Kubiczek36/TKC/imgs/bw_schema_okularu.jpeg

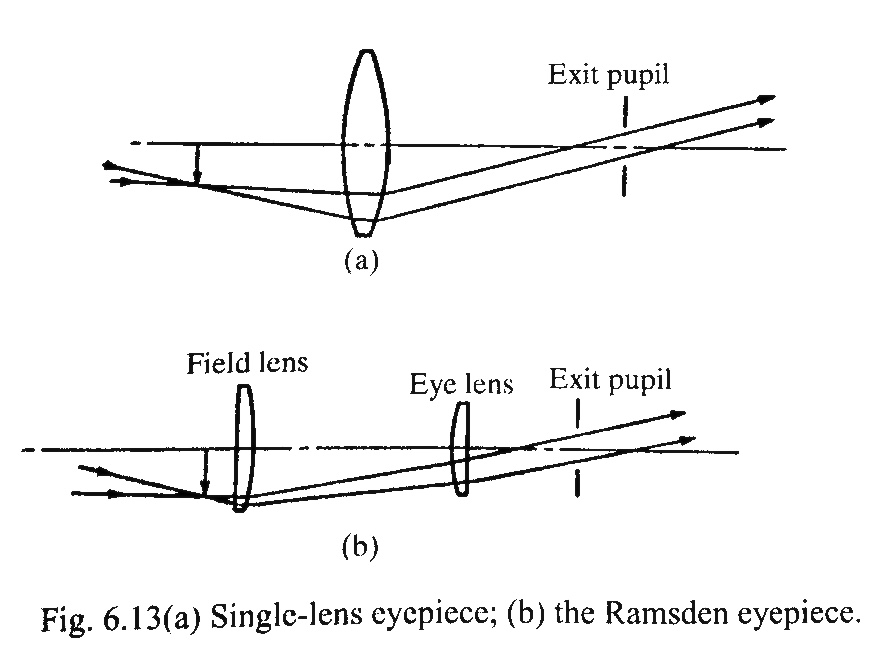
imgs/bw_schema_okularu.jpeg
