Kubiczek36/TKC/imgs/clony.png

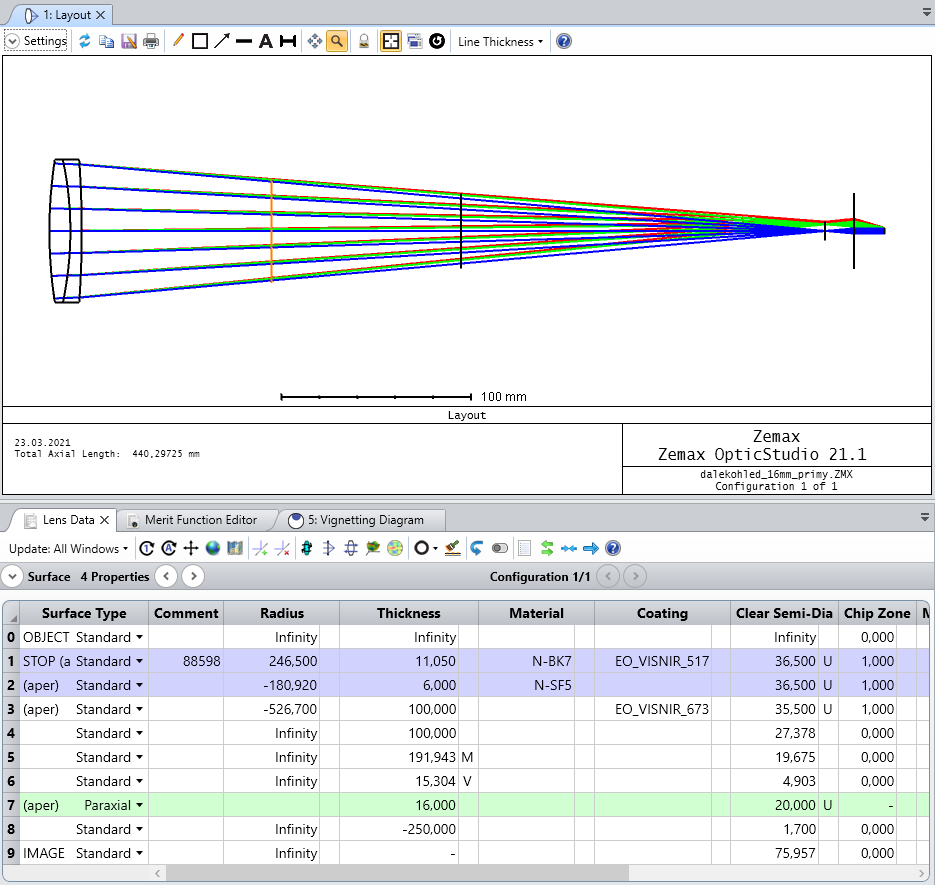
imgs/clony.png
