Kubiczek36/TKC/imgs/clony_1.png

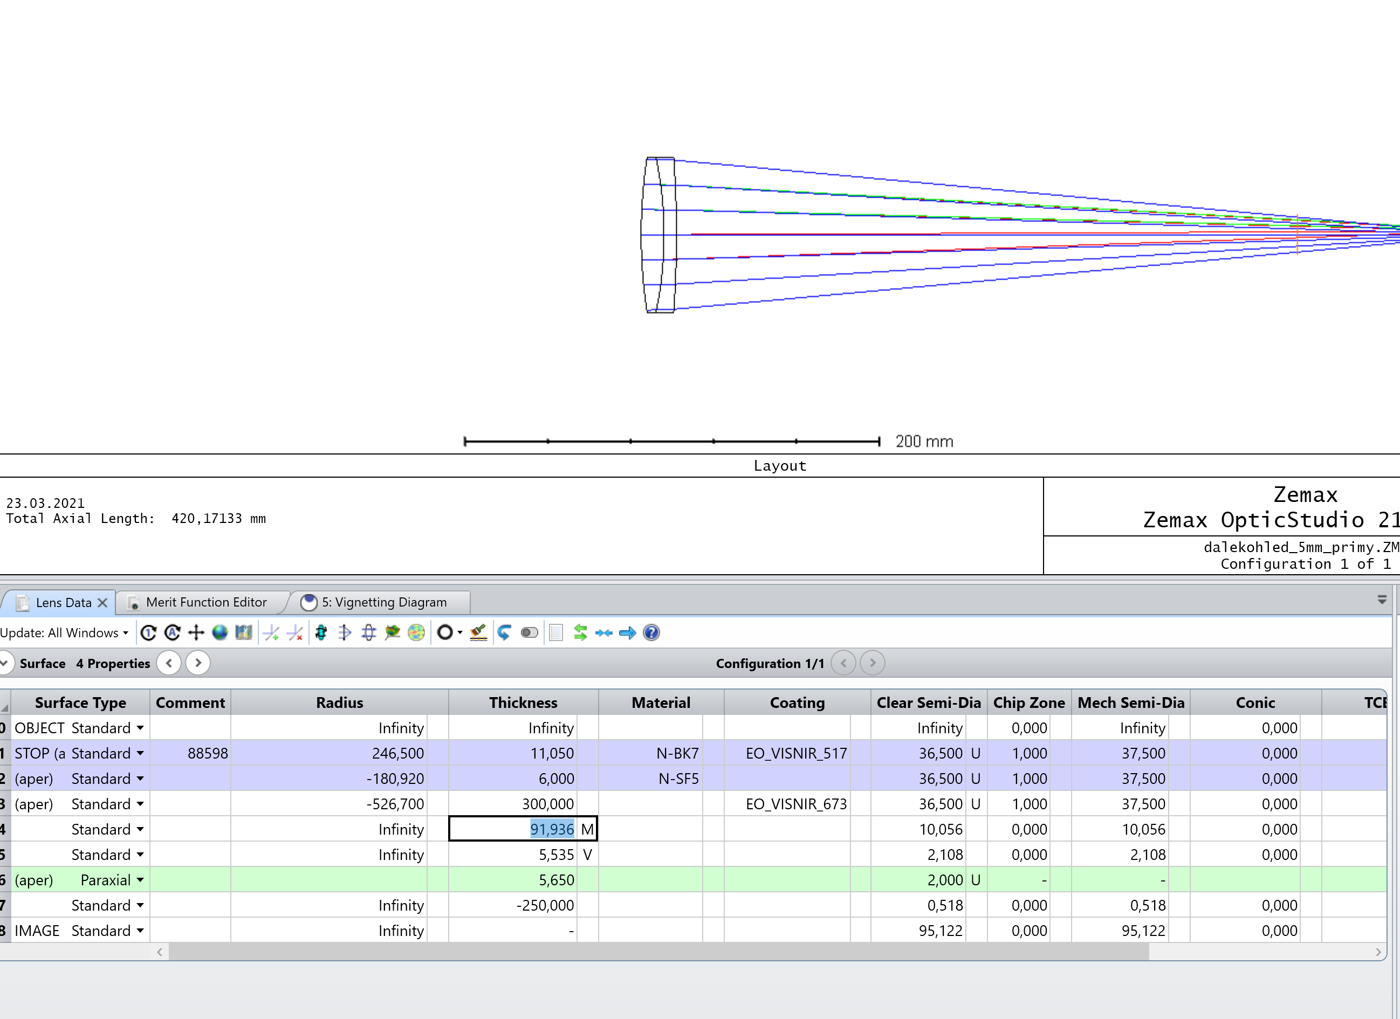
imgs/clony_1.png
