Kubiczek36/TKC/imgs/FFTMTF_5mm.png

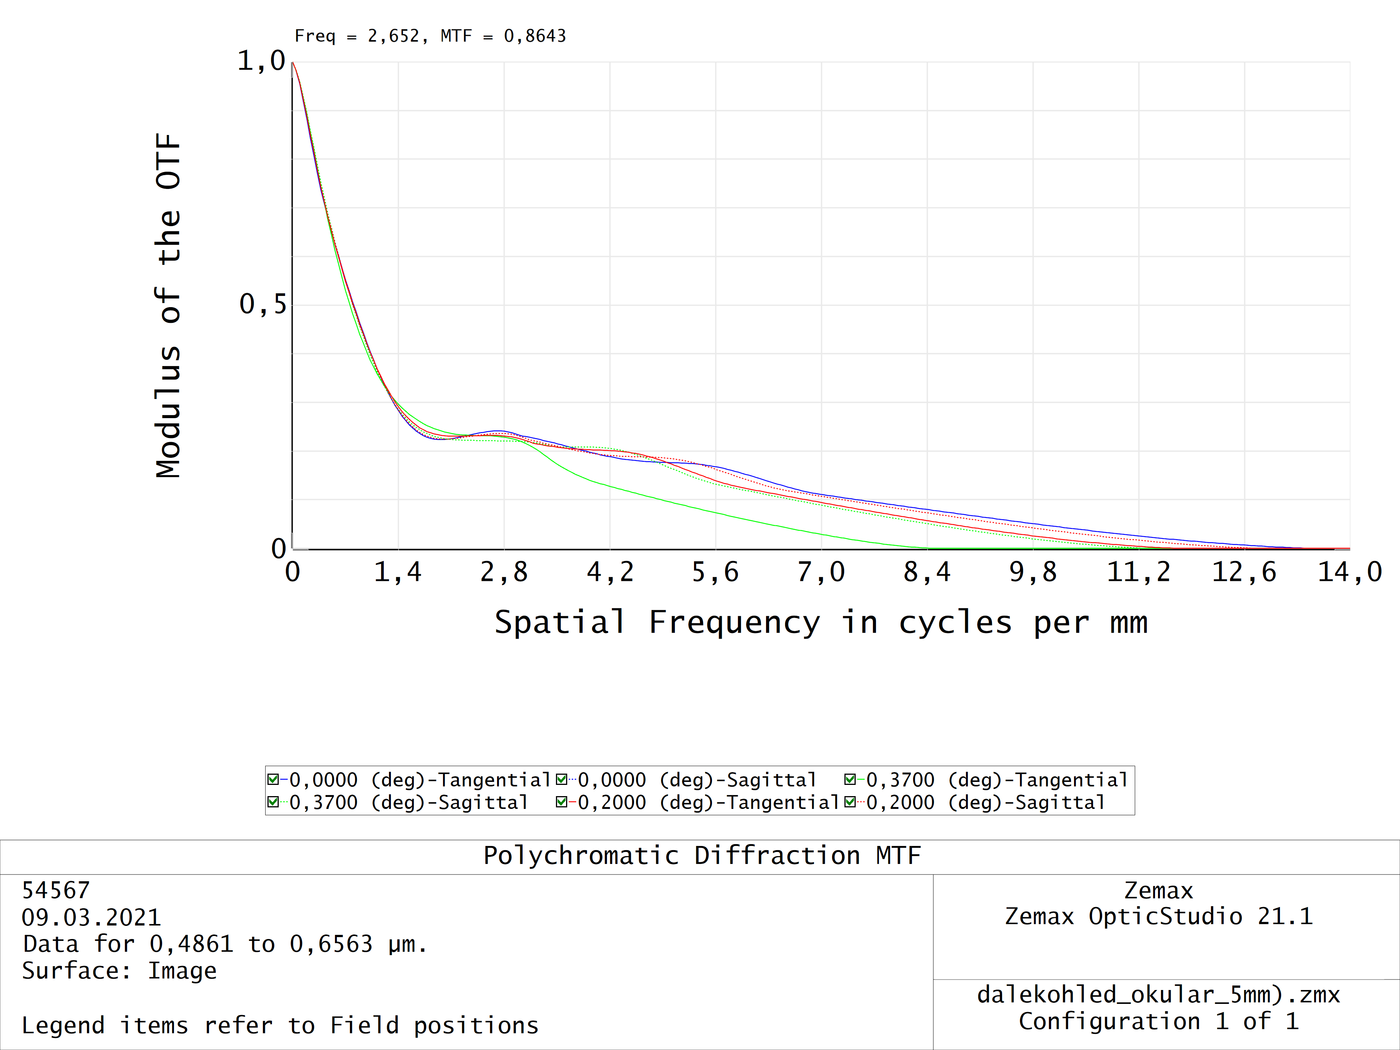
imgs/FFTMTF_5mm.png
