Kubiczek36/TKC/imgs/FFTMTFvsField_dublet_prez.png

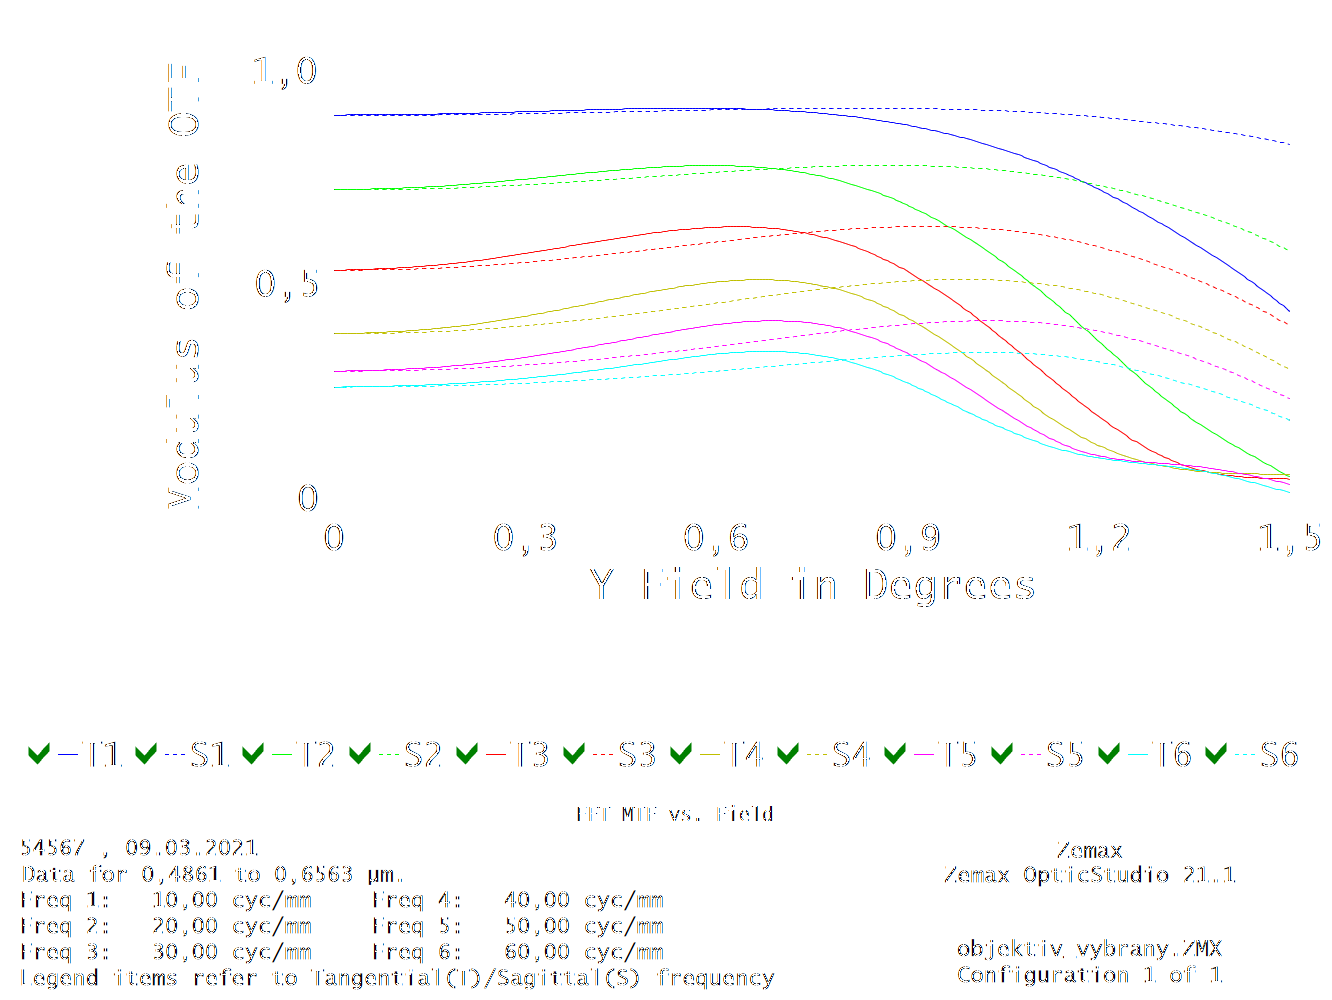
imgs/FFTMTFvsField_dublet_prez.png
