Kubiczek36/TKC/imgs/fh_dalekohledove_ok.jpeg

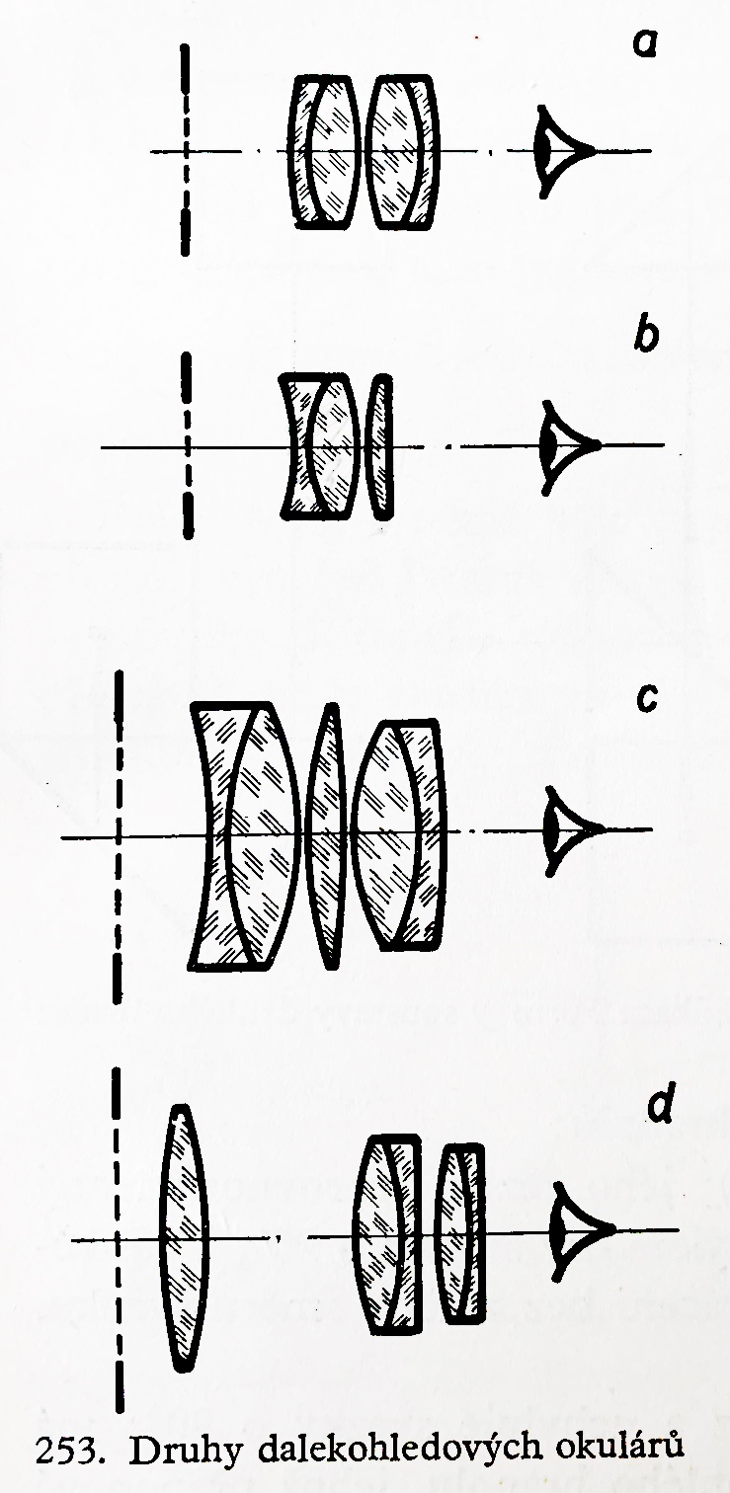
imgs/fh_dalekohledove_ok.jpeg
