Kubiczek36/TKC/imgs/fh_mikroskopove_okulary.jpeg

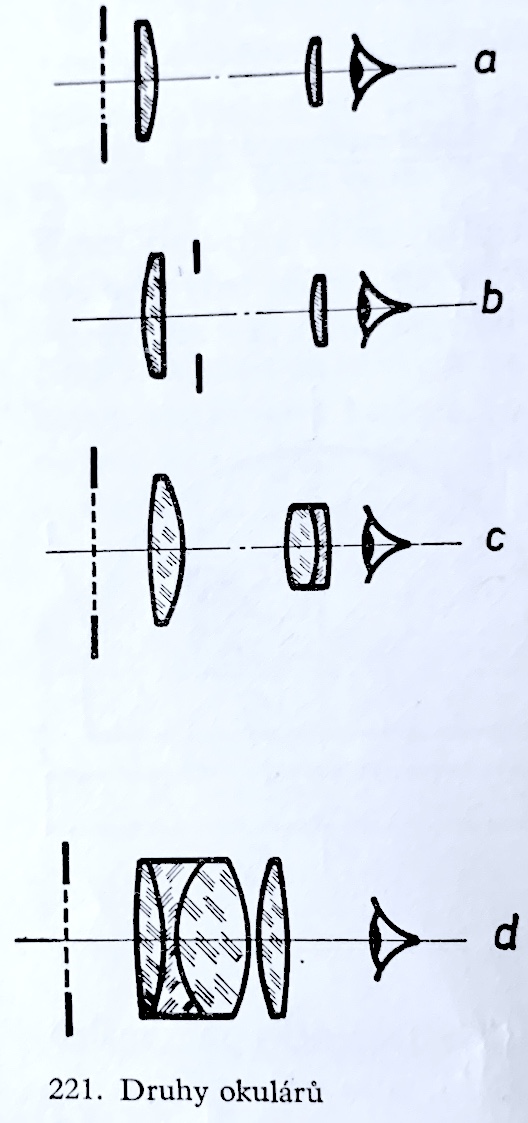
imgs/fh_mikroskopove_okulary.jpeg
