Kubiczek36/TKC/imgs/field_curv_prez.png

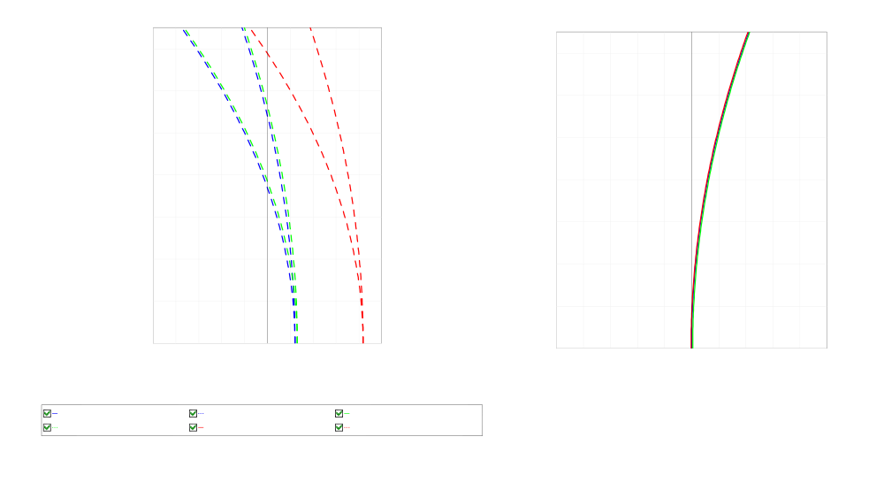
imgs/field_curv_prez.png
