Kubiczek36/TKC/imgs/Layout.png

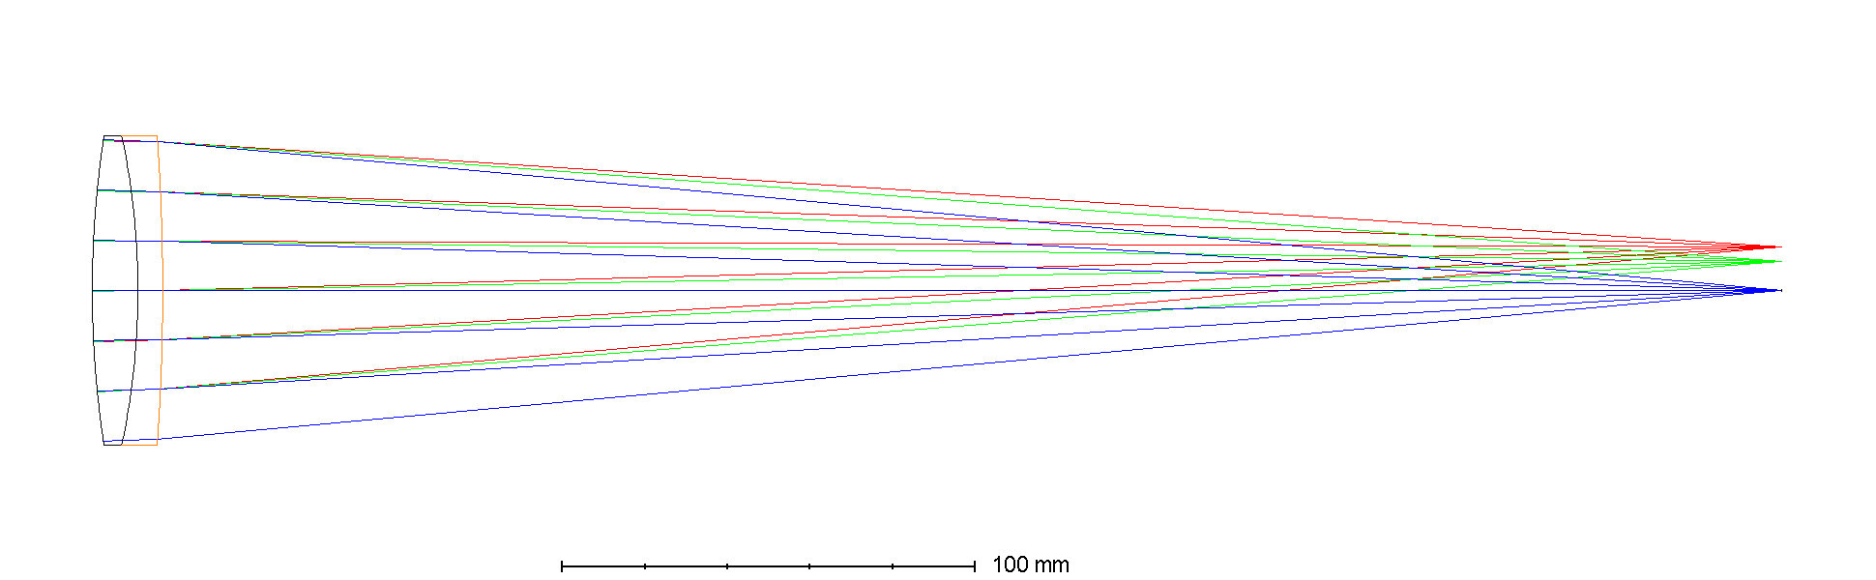
imgs/Layout.png
