Kubiczek36/TKC/imgs/leica_porovnani.png

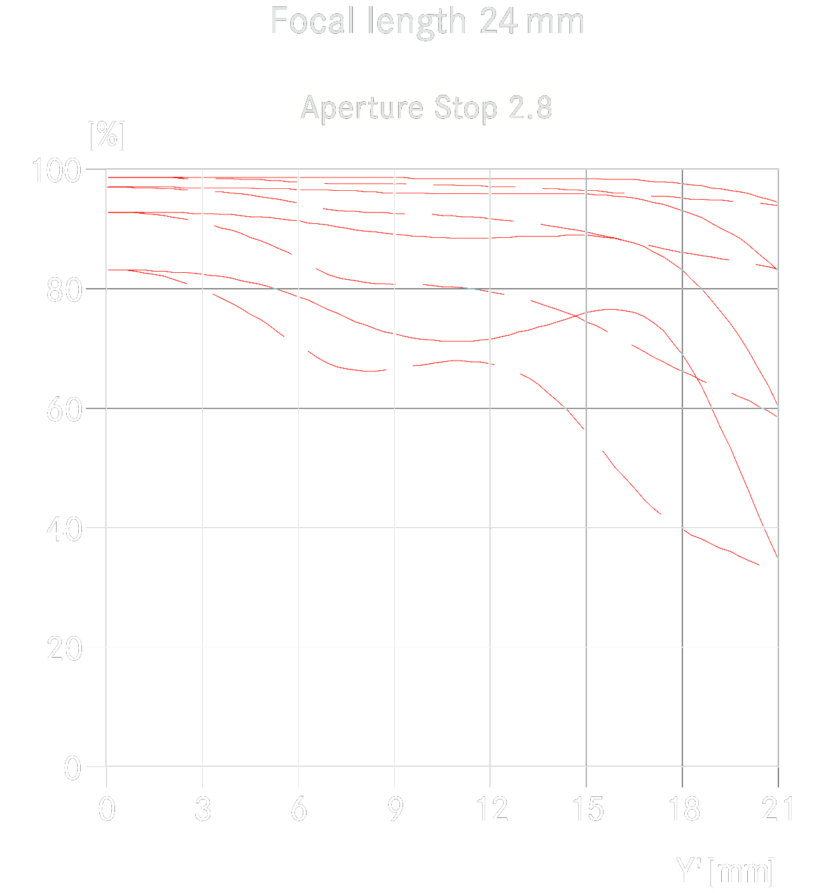
imgs/leica_porovnani.png
