Kubiczek36/TKC/imgs/nakres.jpg

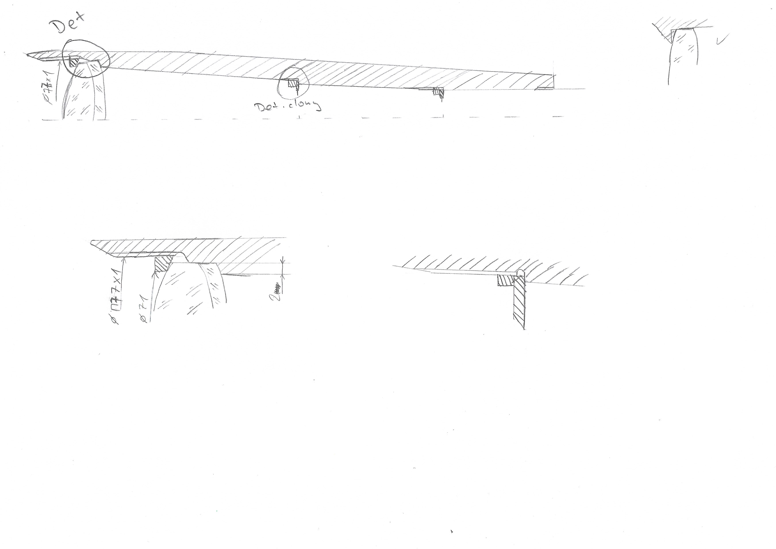
imgs/nakres.jpg
