Kubiczek36/TKC/imgs/preview.JPG

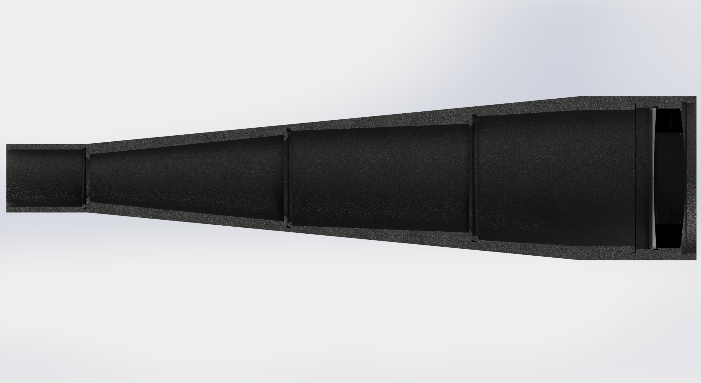
imgs/preview.JPG
