Kubiczek36/TKC/imgs/render_4.JPG

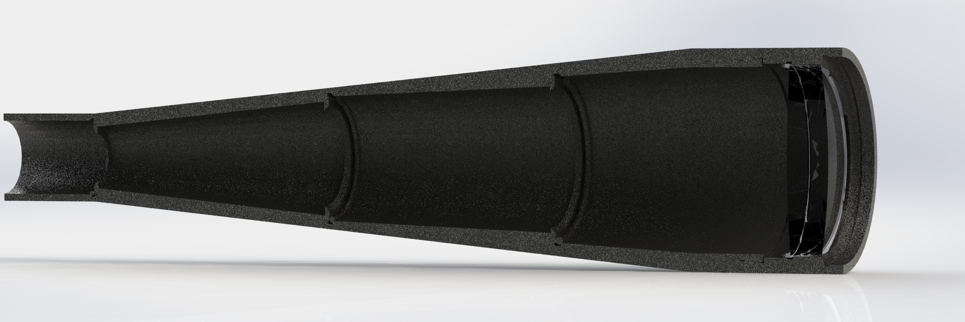
imgs/render_4.JPG
