Kubiczek36/TKC/imgs/render_6.JPG

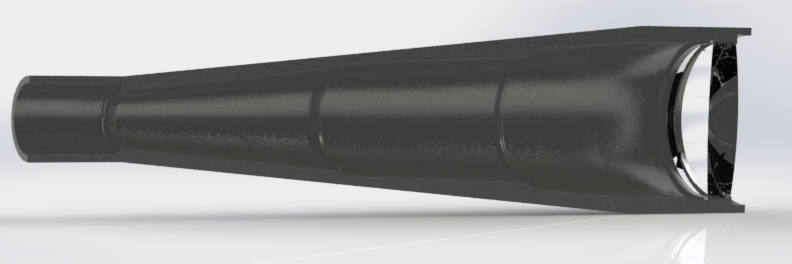
imgs/render_6.JPG
