Kubiczek36/TKC/imgs/render_7.JPG

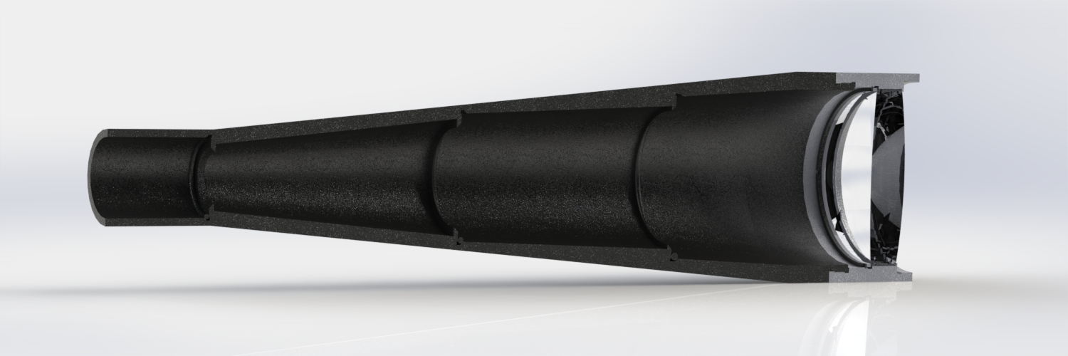
imgs/render_7.JPG
