Kubiczek36/TKC/imgs/render_final_foto.png

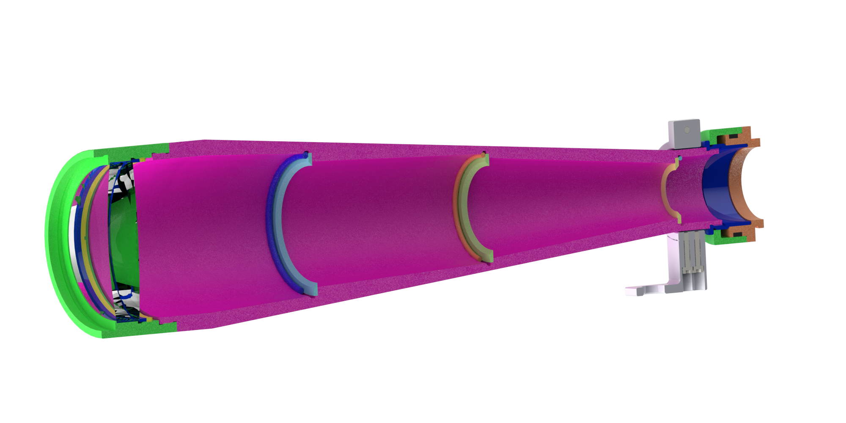
imgs/render_final_foto.png
