Kubiczek36/TKC/imgs/render_final_oko.png

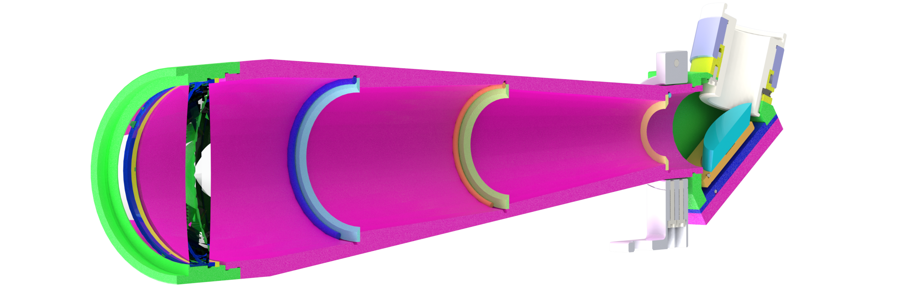
imgs/render_final_oko.png
