Kubiczek36/TKC/imgs/render_foto_vysuv.png

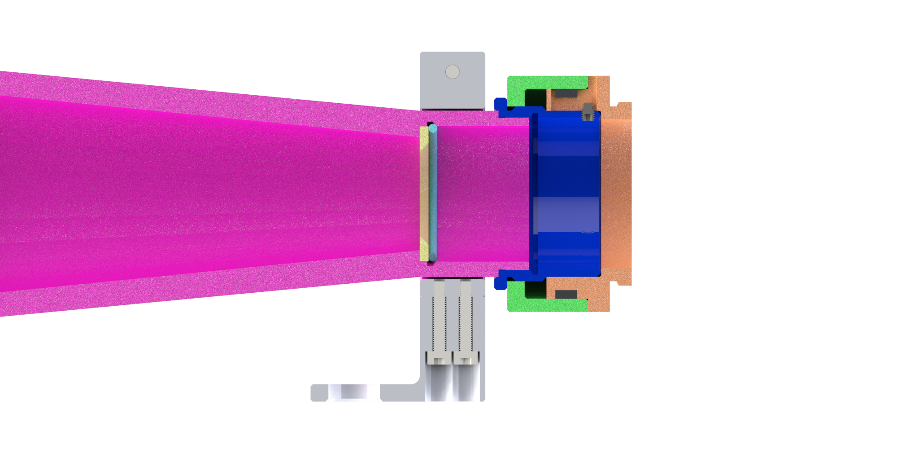
imgs/render_foto_vysuv.png
