Kubiczek36/TKC/imgs/render_tribod_mechanizmus.png

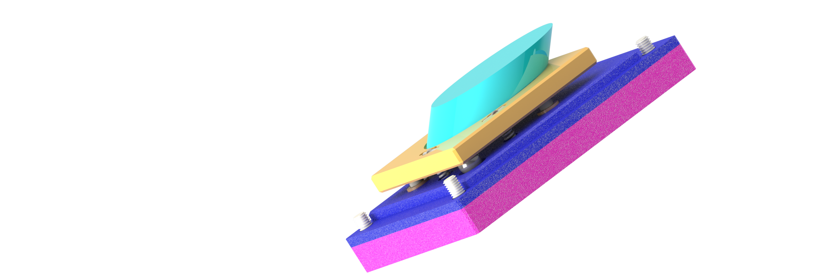
imgs/render_tribod_mechanizmus.png
