Kubiczek36/TKC/imgs/render_vysuv.png

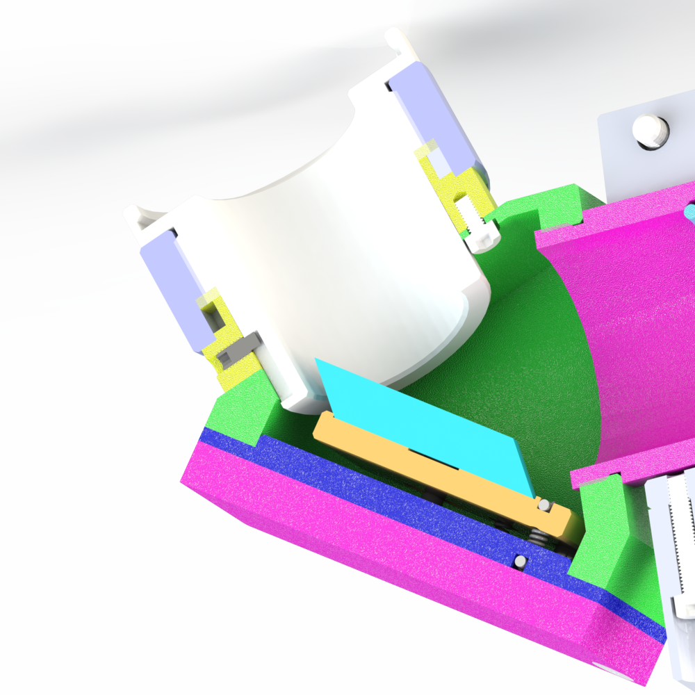
imgs/render_vysuv.png
