Kubiczek36/TKC/imgs/ShadedModel.png

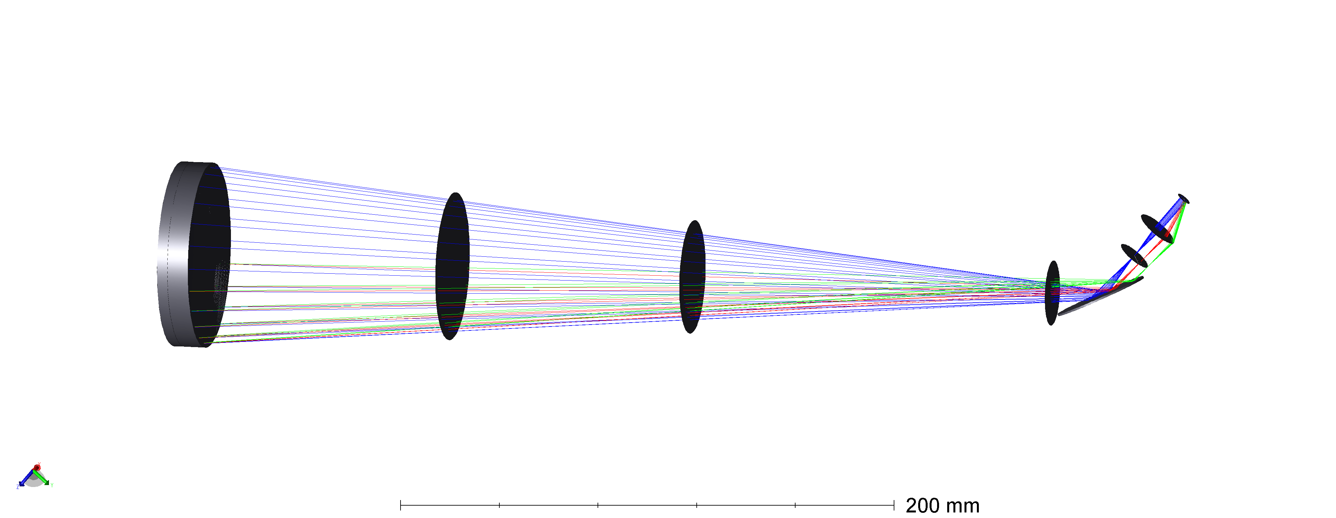
imgs/ShadedModel.png
