Kubiczek36/TKC/imgs/ShadedModel_1.png

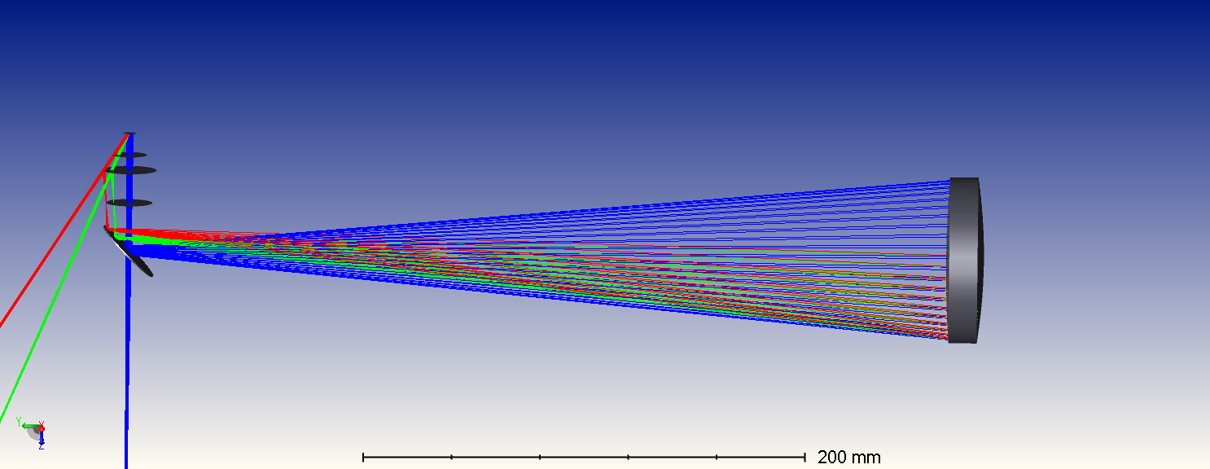
imgs/ShadedModel_1.png
