Kubiczek36/TKC/imgs/ShadedModel_high_res.png

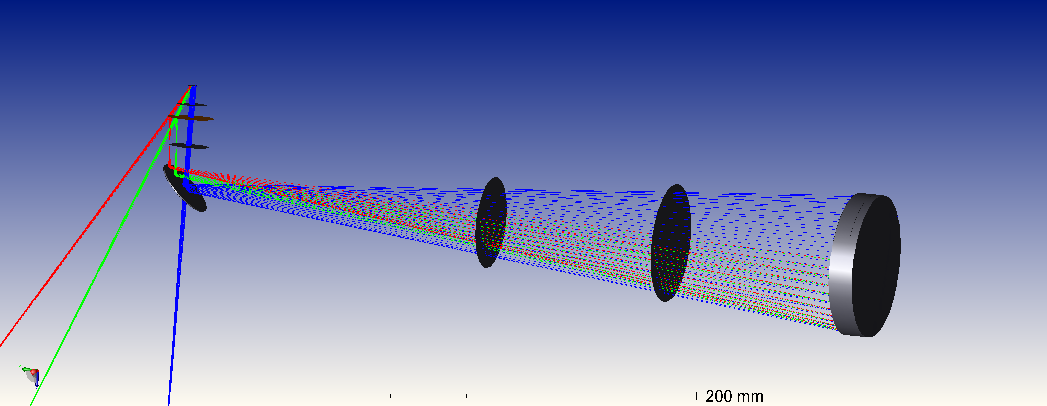
imgs/ShadedModel_high_res.png
