Kubiczek36/TKC/imgs/SpotDiagram_5_mm.png

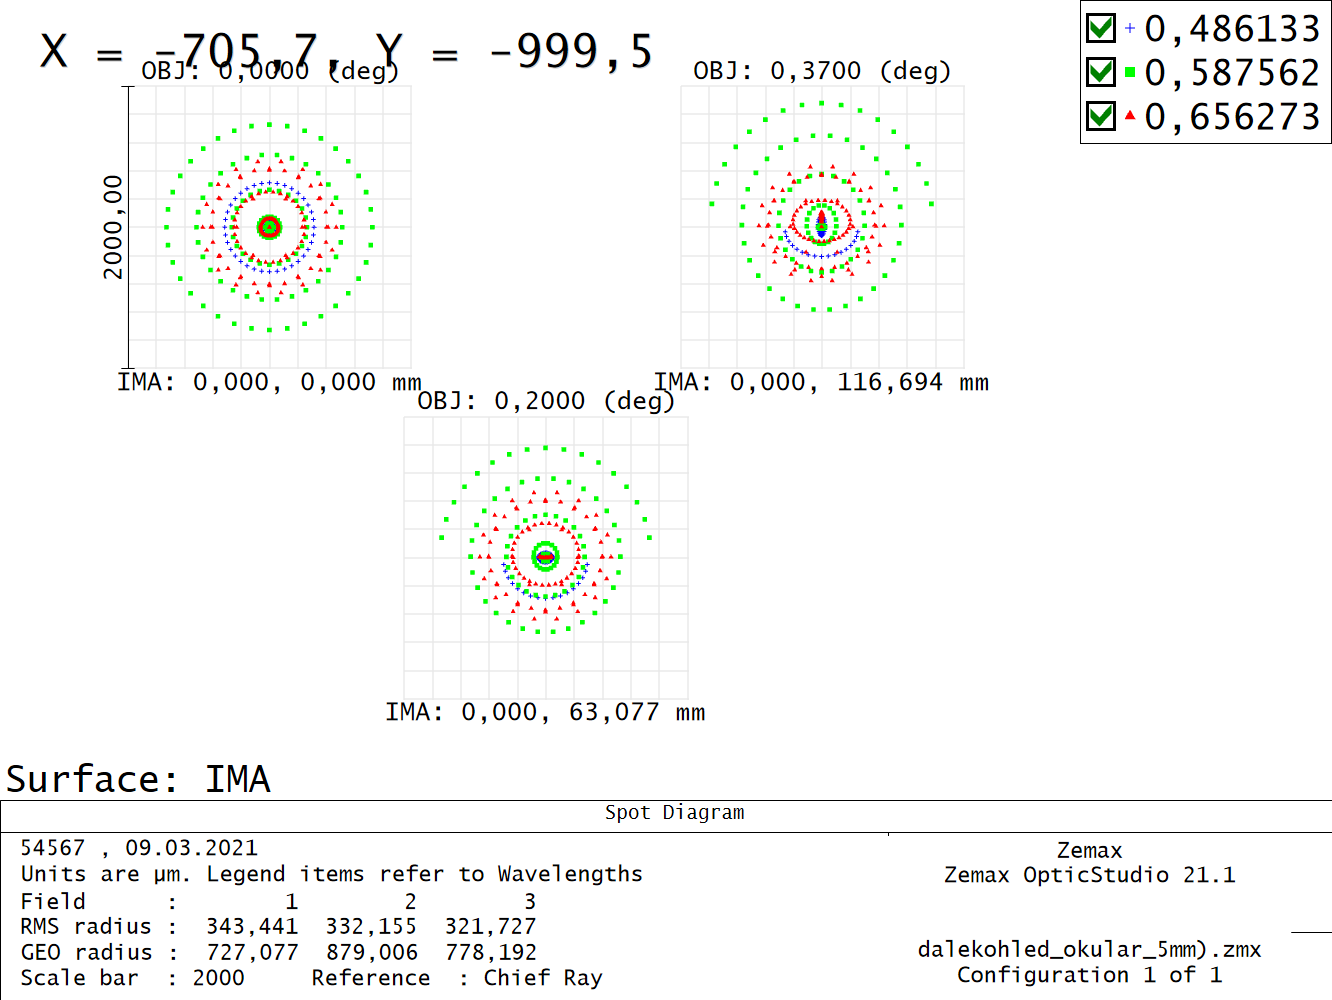
imgs/SpotDiagram_5_mm.png
