Kubiczek36/TKC/imgs/SpotDiagram_obraz_objektivu.png

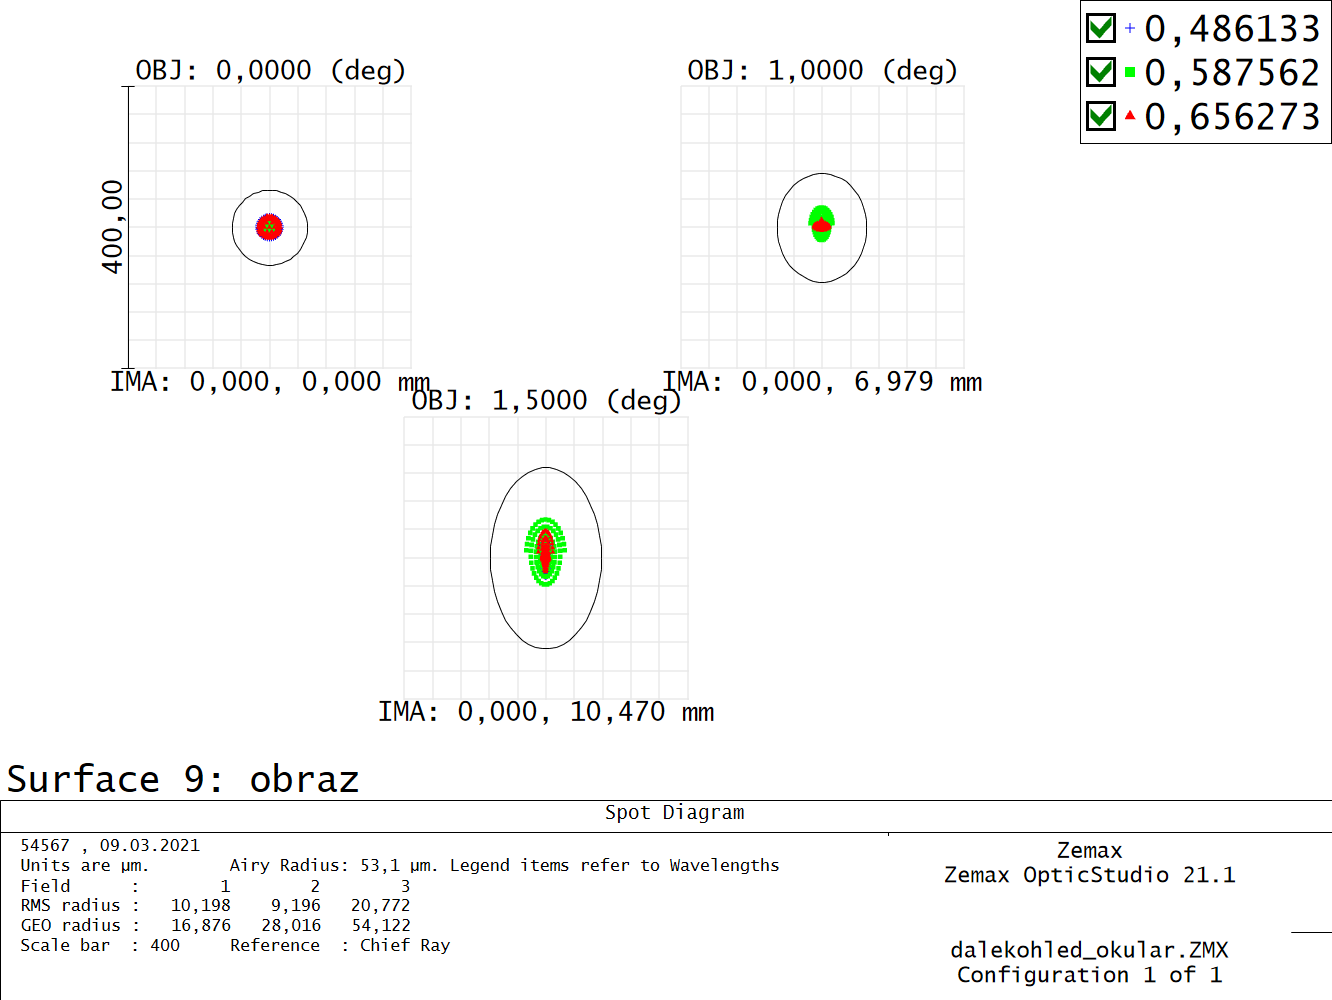
imgs/SpotDiagram_obraz_objektivu.png
