Kubiczek36/TKC/imgs/tubus_+_objektiv_+_polotovary.jpg

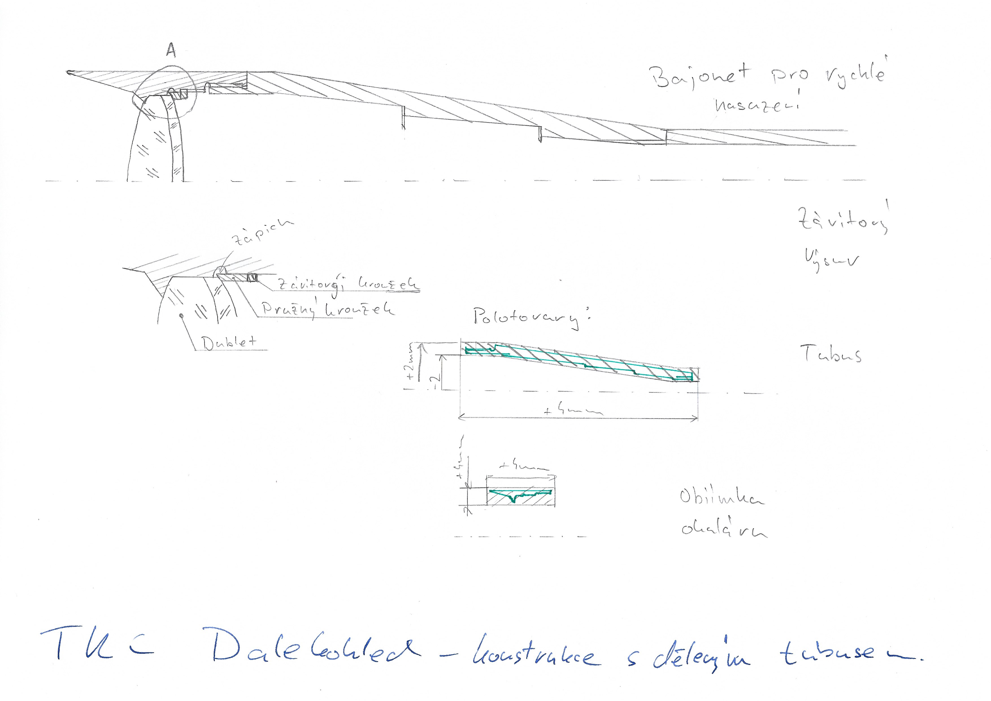
imgs/tubus_+_objektiv_+_polotovary.jpg
