Kubiczek36/TKC/imgs/tubus_s_objektivovou_objimkou.jpg

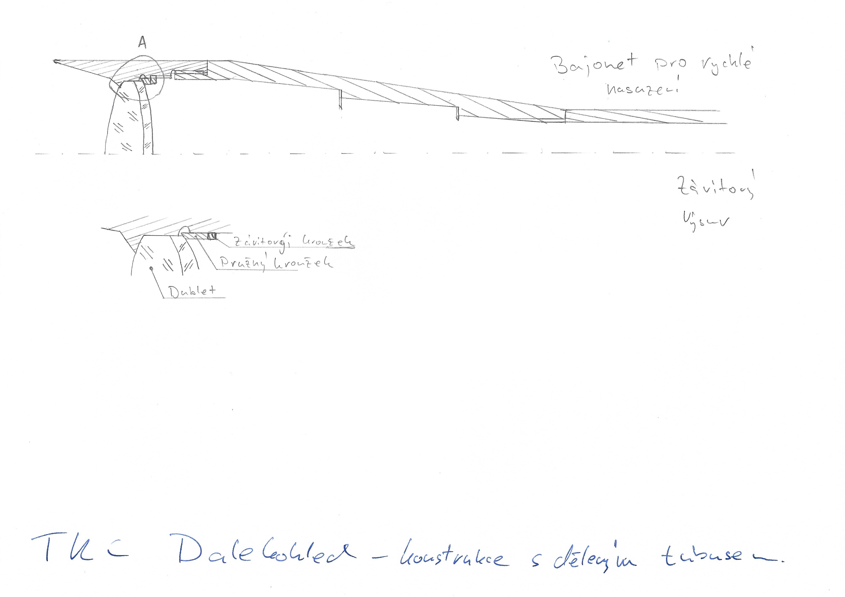
imgs/tubus_s_objektivovou_objimkou.jpg
