Kubiczek36/TKC/imgs/uchyceni zrcatka.png

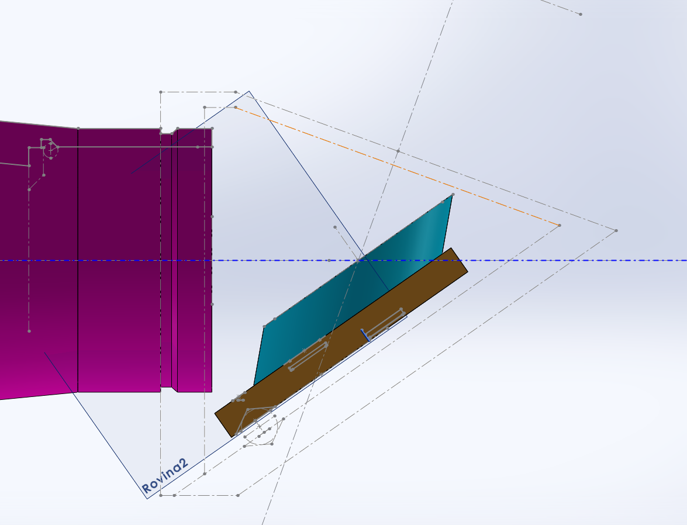
imgs/uchyceni zrcatka.png
