Kubiczek36/TKC/imgs/ulozeni_zrcatka_1.png

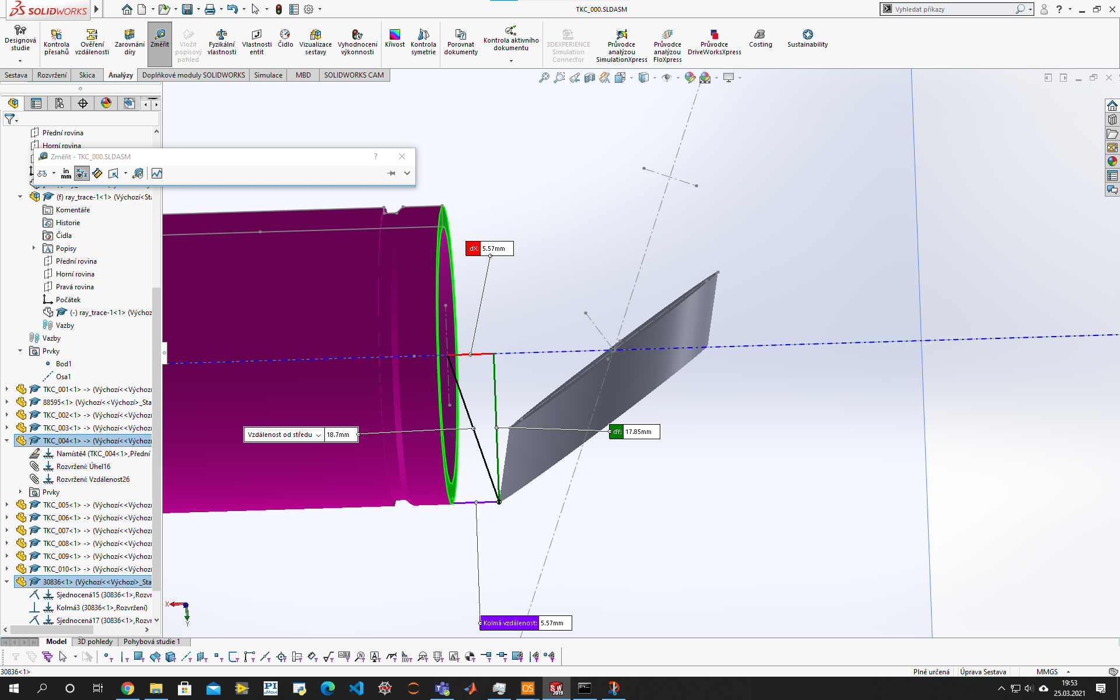
imgs/ulozeni_zrcatka_1.png
