Kubiczek36/TKC/imgs/zavitovy_vysuv.png

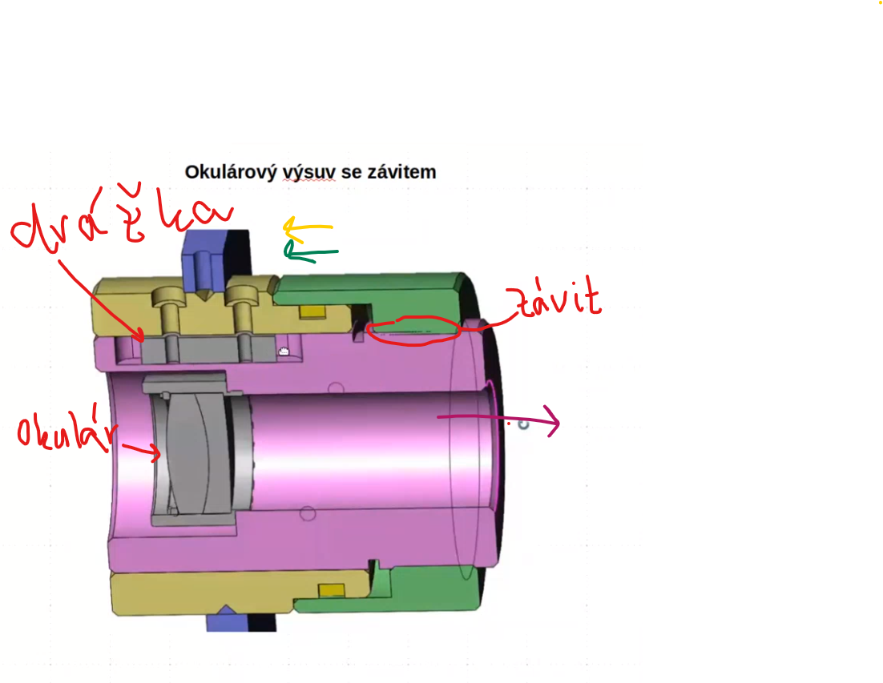
imgs/zavitovy_vysuv.png
