Kubiczek36/TKC/zemax/Okuláry/Moon.bmp

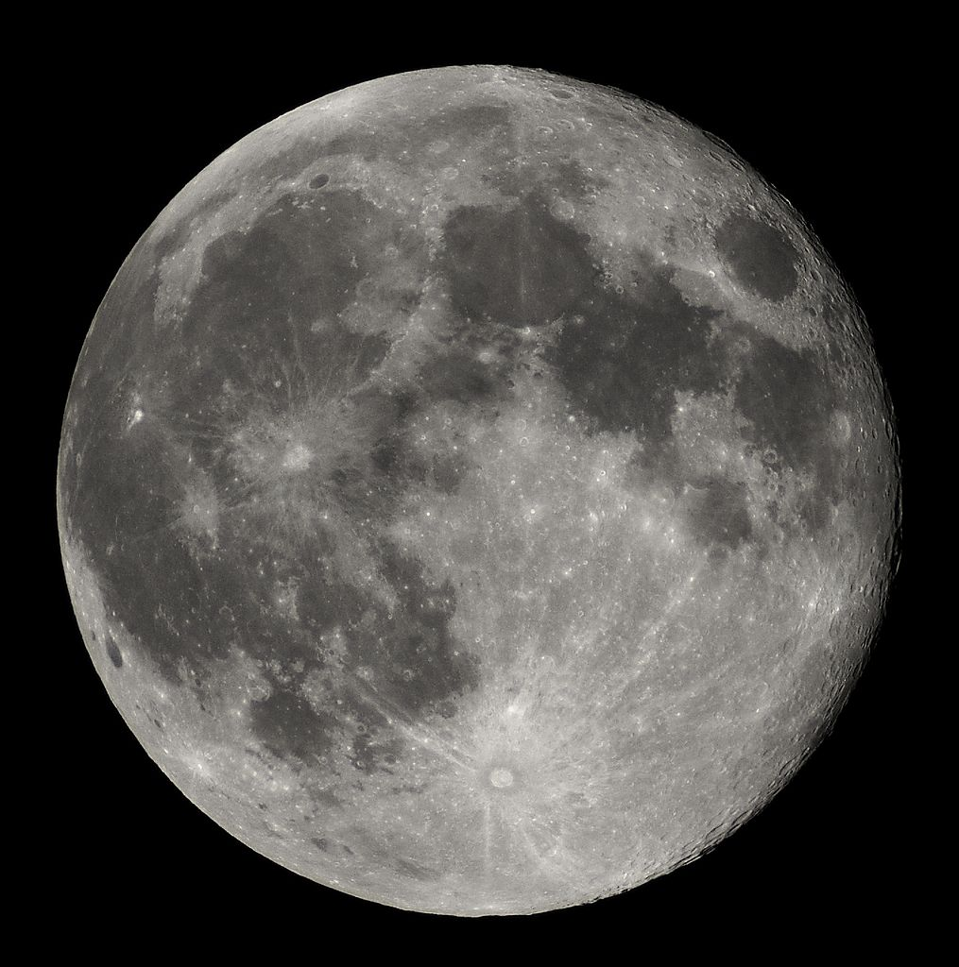
zemax/Okuláry/Moon.bmp
