Kubiczek36/TKC/CAD/TKC_016.SLDPRT

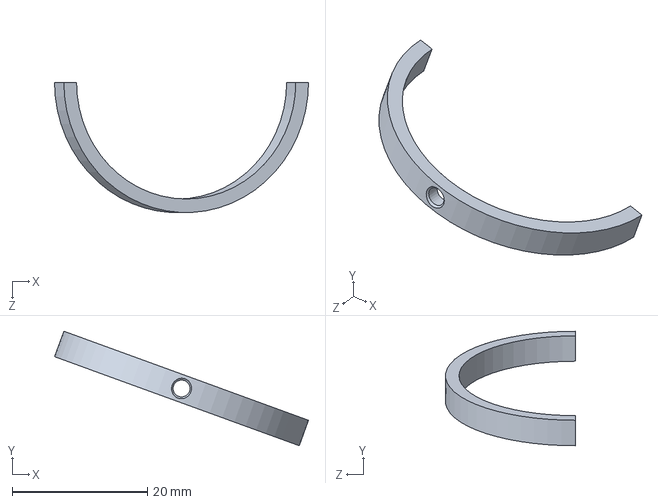
[picture p66: CAD file, 2021-05-25]
CAD/TKC_016.SLDPRT
37.5 x 16.9 x 19.2 mm
