Kubiczek36/TKC/CAD/TKC_014.SLDPRT

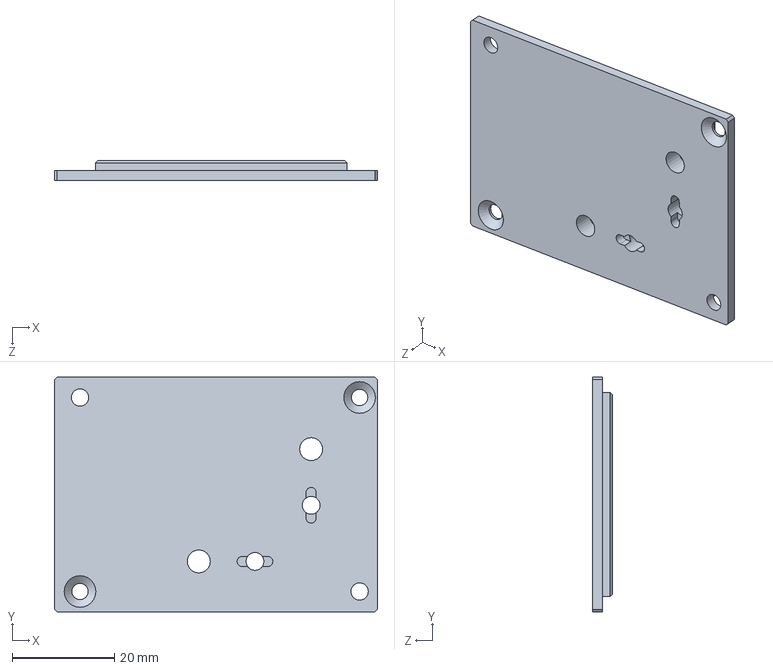
[picture p67: CAD file, 2021-05-25]
CAD/TKC_014.SLDPRT
63.3 x 46.0 x 4.00 mm
