Kubiczek36/TKC/CAD/TKC_020.SLDPRT

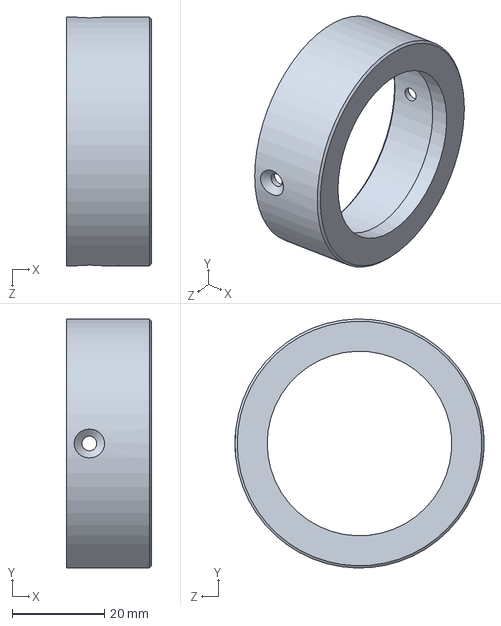
[picture p68: CAD file, 2021-05-25]
CAD/TKC_020.SLDPRT
18.5 x 54.0 x 54.0 mm
