Kubiczek36/TKC/CAD/TKC_023.SLDPRT

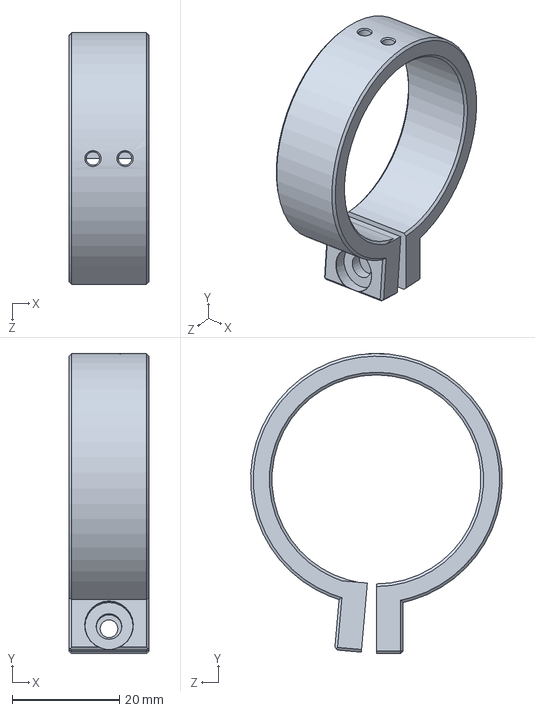
[picture p69: CAD file, 2021-05-25]
CAD/TKC_023.SLDPRT
15.0 x 56.0 x 47.0 mm
