Kubiczek36/TKC/CAD/TKC_011.SLDPRT

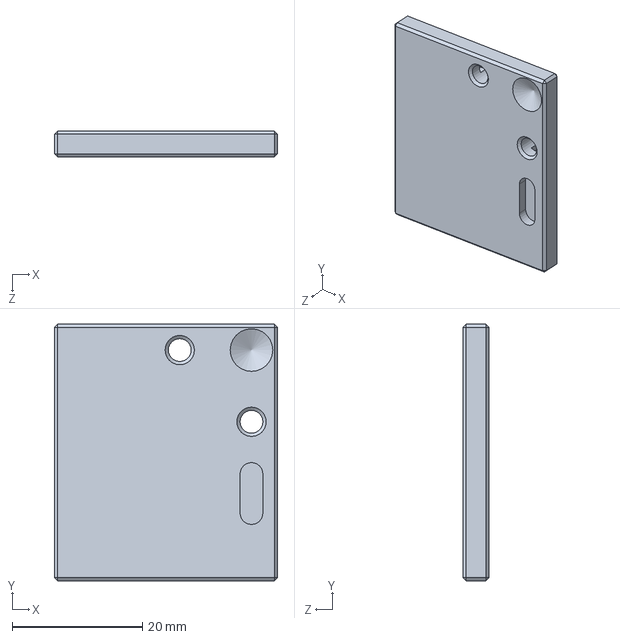
[picture p70: CAD file, 2021-05-25]
CAD/TKC_011.SLDPRT
34.2 x 39.4 x 4.00 mm
