Kubiczek36/TKC/CAD/TKC_012.SLDPRT

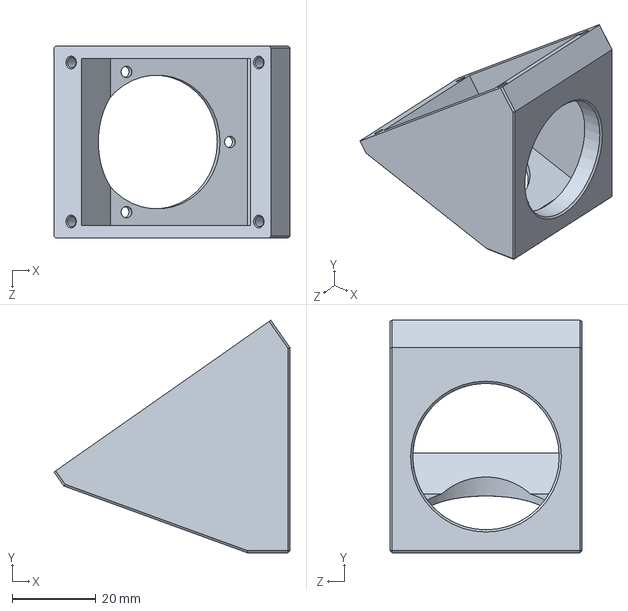
[picture p71: CAD file, 2021-05-25]
CAD/TKC_012.SLDPRT
56.4 x 55.6 x 46.0 mm
