Kubiczek36/TKC/CAD/TKC_015.SLDPRT

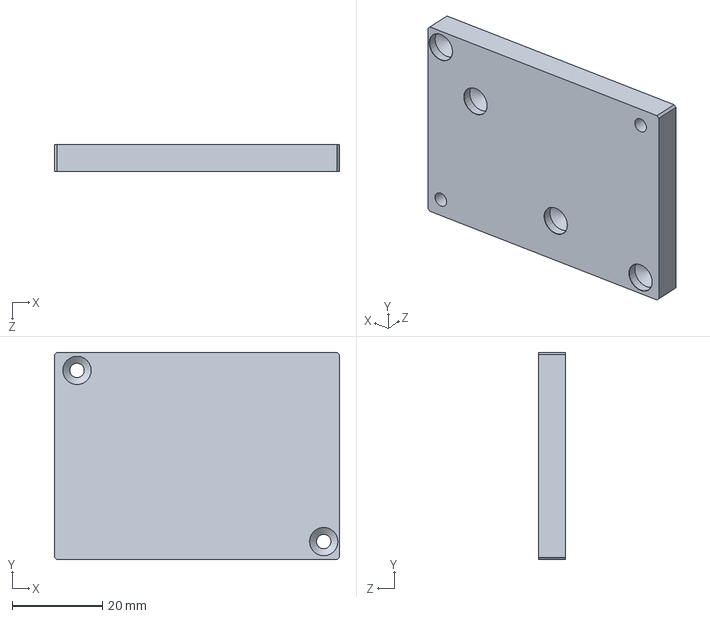
[picture p72: CAD file, 2021-05-25]
CAD/TKC_015.SLDPRT
63.3 x 46.0 x 6.00 mm
