Kubiczek36/TKC/CAD/dalekohled_okular_5mm_ray_trace.stp

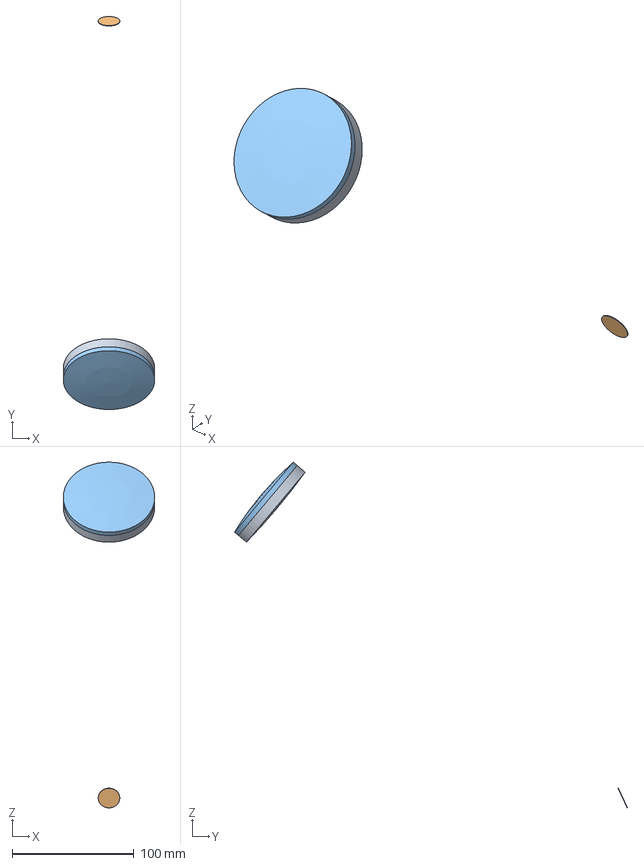
[picture p73: CAD file, 2021-05-25]
CAD/dalekohled_okular_5mm_ray_trace.stp
75.0 x 322.5 x 283.7 mm
surfaces 2,3
mirror 5
surfaces 1,2
