Kubiczek36/TKC/CAD/TKC_004.SLDPRT

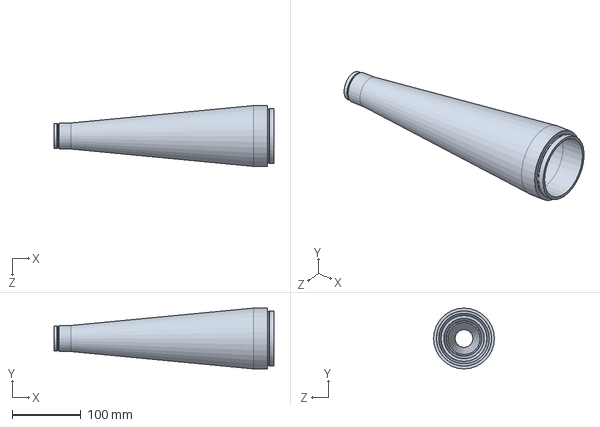
[picture p74: CAD file, 2021-05-25]
CAD/TKC_004.SLDPRT
319.8 x 88.5 x 88.5 mm
