Kubiczek36/TKC/CAD/TKC_006.SLDPRT

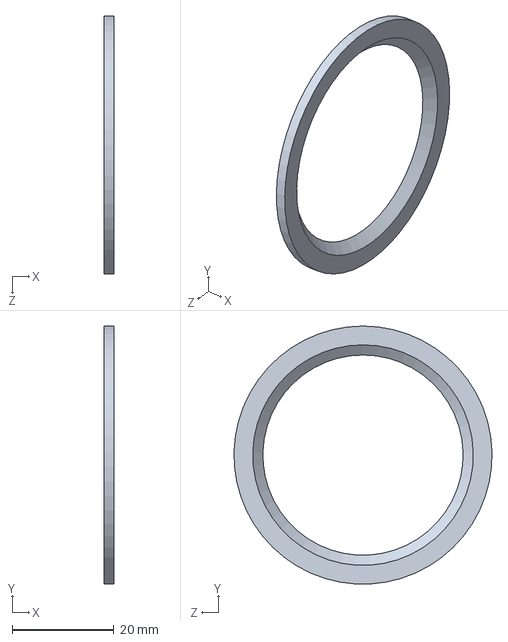
[picture p75: CAD file, 2021-05-25]
CAD/TKC_006.SLDPRT
2.00 x 50.8 x 50.8 mm
