Kubiczek36/TKC/CAD/TKC_024.SLDPRT

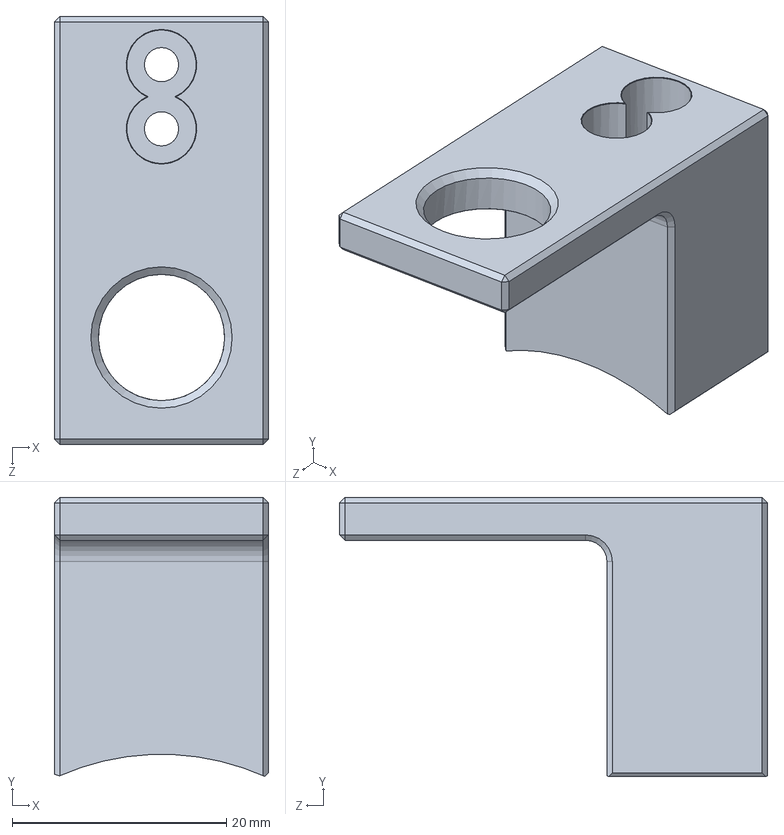
[picture p76: CAD file, 2021-05-25]
CAD/TKC_024.SLDPRT
20.0 x 26.1 x 40.0 mm
