Kubiczek36/TKC/CAD/TKC_022.SLDPRT

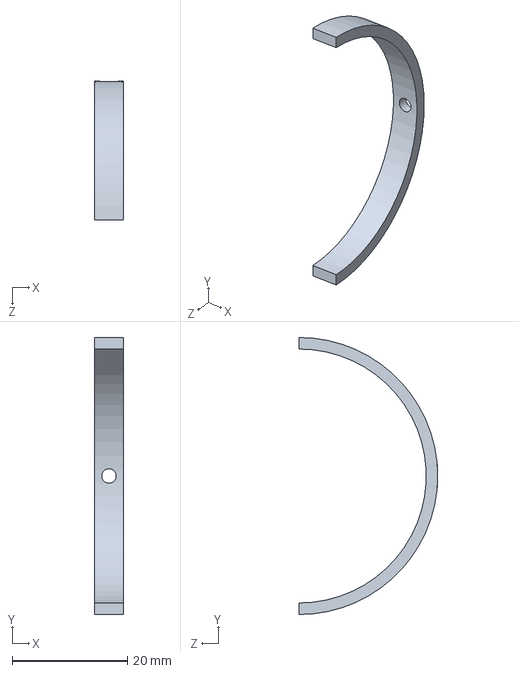
[picture p77: CAD file, 2021-05-25]
CAD/TKC_022.SLDPRT
5.00 x 48.0 x 24.0 mm
