Kubiczek36/TKC/CAD/TKC_013.SLDPRT

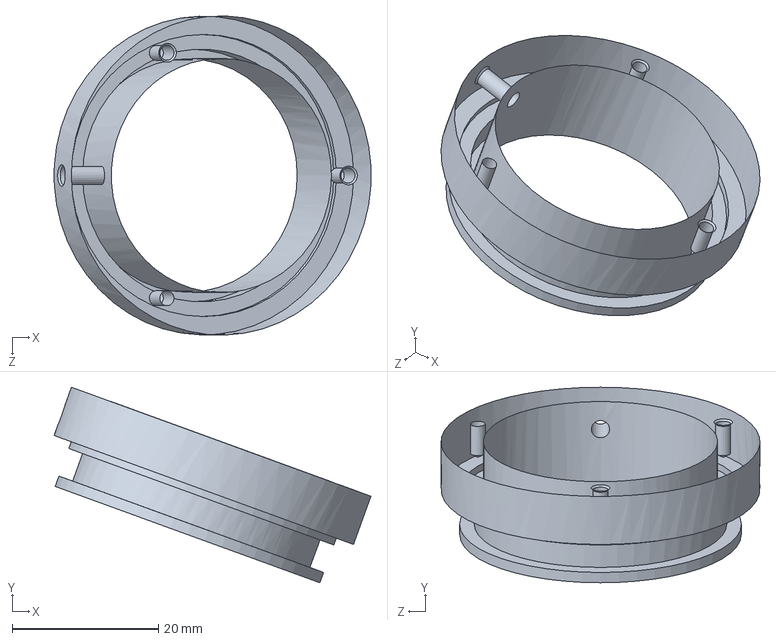
[picture p78: CAD file, 2021-05-25]
CAD/TKC_013.SLDPRT
43.3 x 26.7 x 43.6 mm
