Kubiczek36/TKC/CAD/TKC_007.SLDPRT

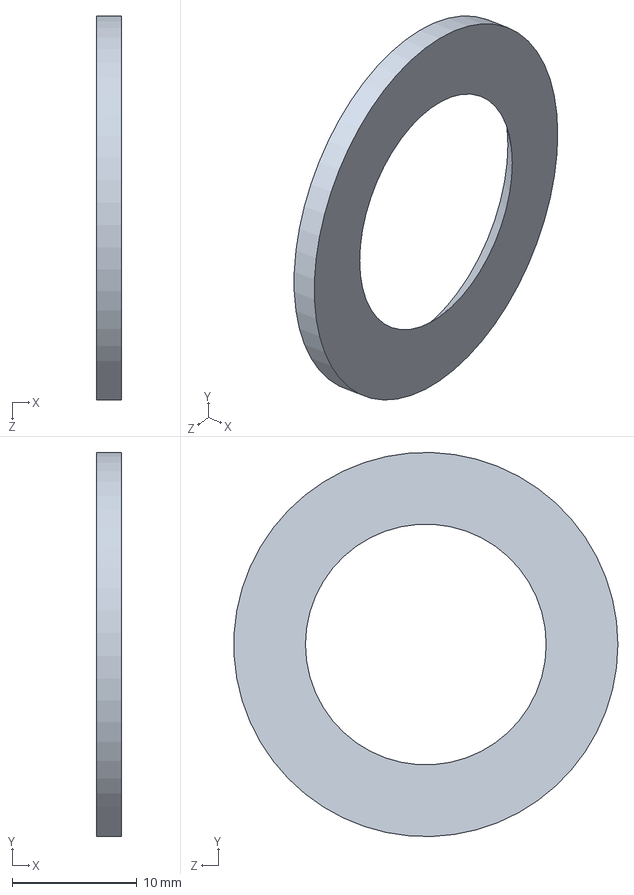
[picture p79: CAD file, 2021-05-25]
CAD/TKC_007.SLDPRT
2.00 x 30.8 x 30.8 mm
