Kubiczek36/TKC/CAD/TKC_005.SLDPRT

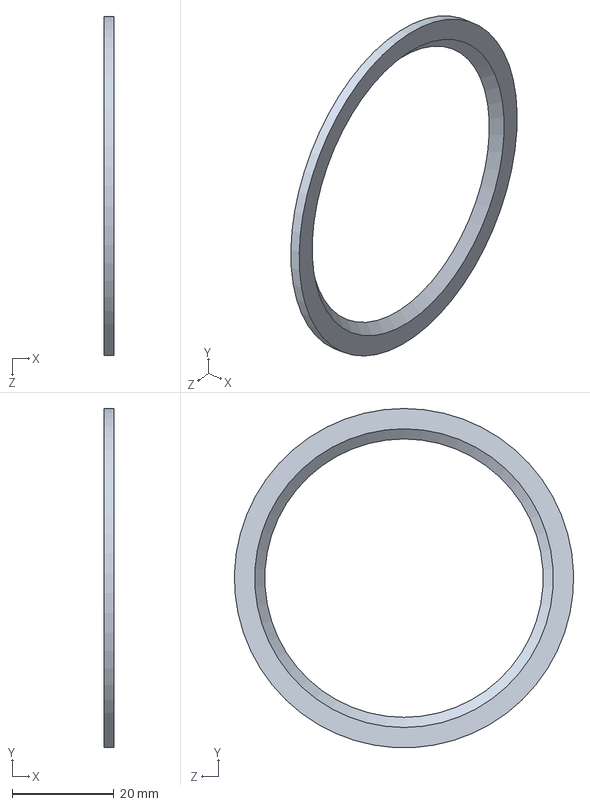
[picture p80: CAD file, 2021-05-25]
CAD/TKC_005.SLDPRT
2.00 x 66.7 x 66.8 mm
