Kubiczek36/TKC/CAD/TKC_010.SLDPRT

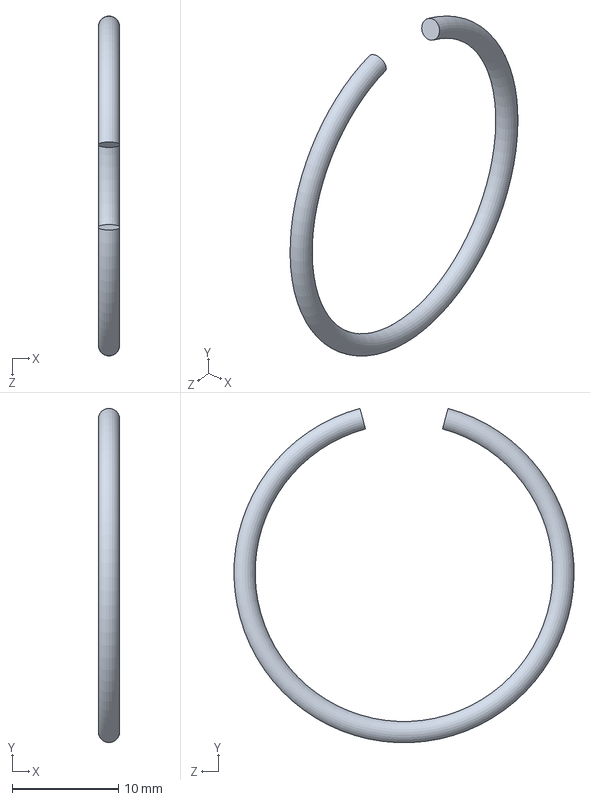
[picture p81: CAD file, 2021-05-25]
CAD/TKC_010.SLDPRT
2.00 x 31.4 x 32.0 mm
