Kubiczek36/TKC/CAD/TKC_008.SLDPRT

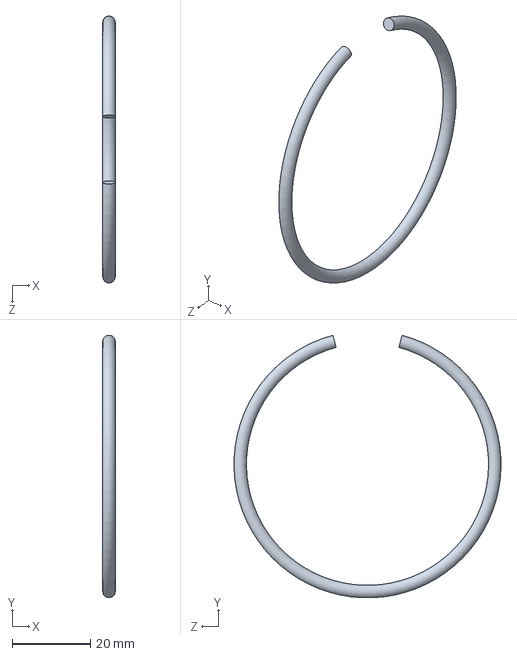
[picture p82: CAD file, 2021-05-25]
CAD/TKC_008.SLDPRT
3.20 x 67.0 x 68.2 mm
