Kubiczek36/TKC/CAD/F3SSN1P.sldprt

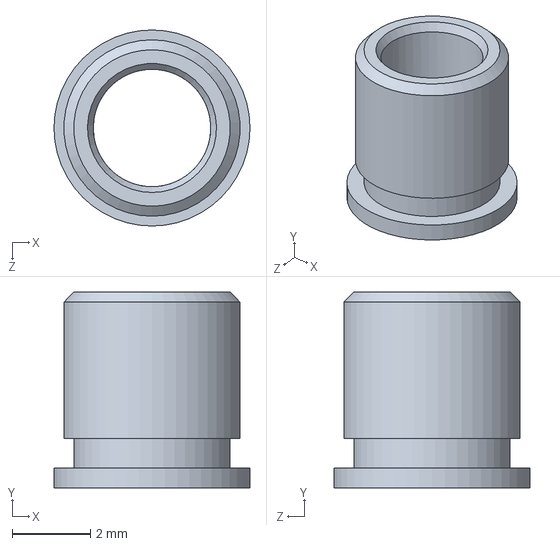
[picture p83: CAD file, 2021-05-25]
CAD/F3SSN1P.sldprt
5.00 x 5.00 x 5.00 mm
