Kubiczek36/TKC/CAD/TKC_021.SLDPRT

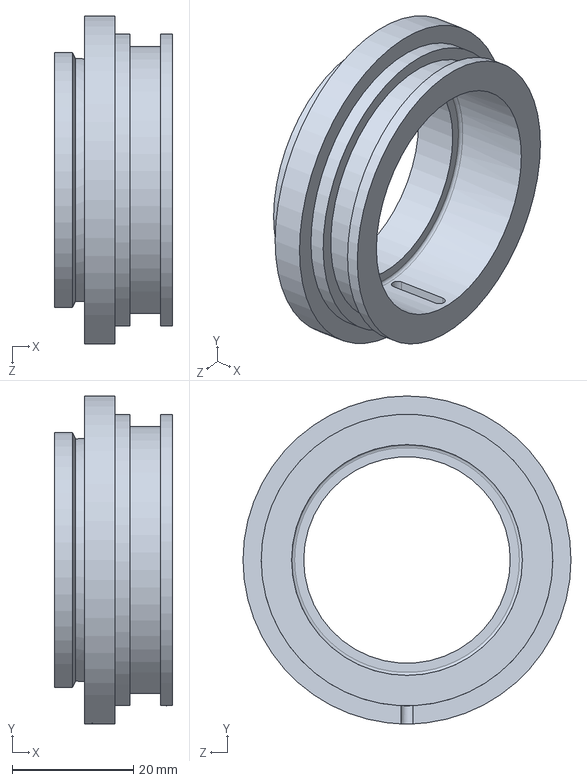
[picture p84: CAD file, 2021-05-25]
CAD/TKC_021.SLDPRT
19.5 x 54.0 x 54.0 mm
