Kubiczek36/TKC/CAD/TKC_002.SLDPRT

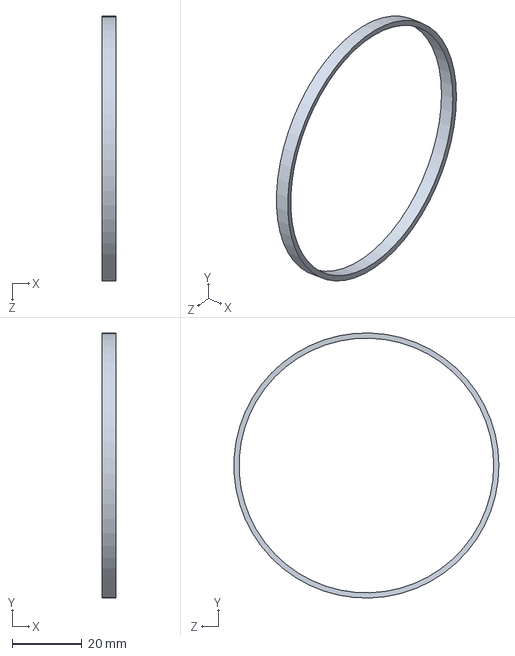
[picture p85: CAD file, 2021-04-27]
CAD/TKC_002.SLDPRT
4.10 x 76.0 x 75.9 mm
