Kubiczek36/TKC/CAD/TKC_001.SLDPRT

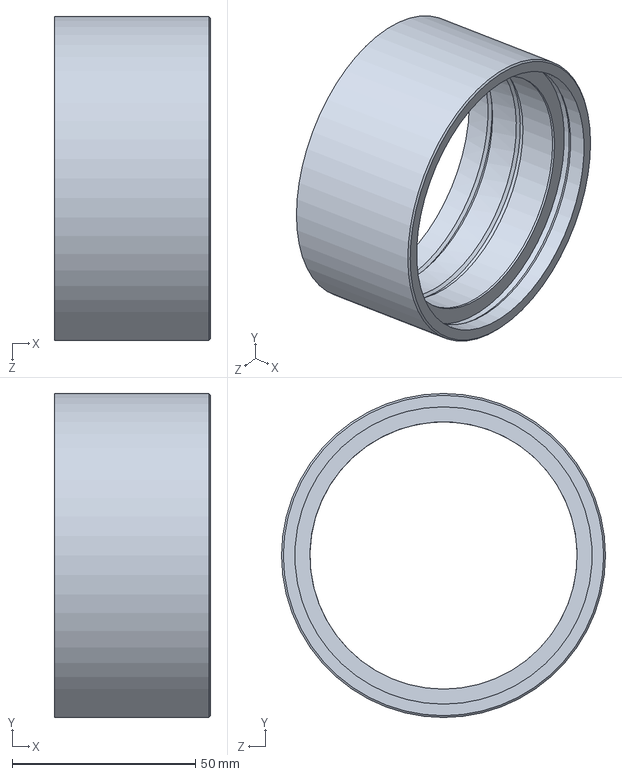
[picture p86: CAD file, 2021-04-27]
CAD/TKC_001.SLDPRT
42.7 x 88.5 x 88.5 mm
