Kubiczek36/TKC/CAD/TKC_003.SLDPRT

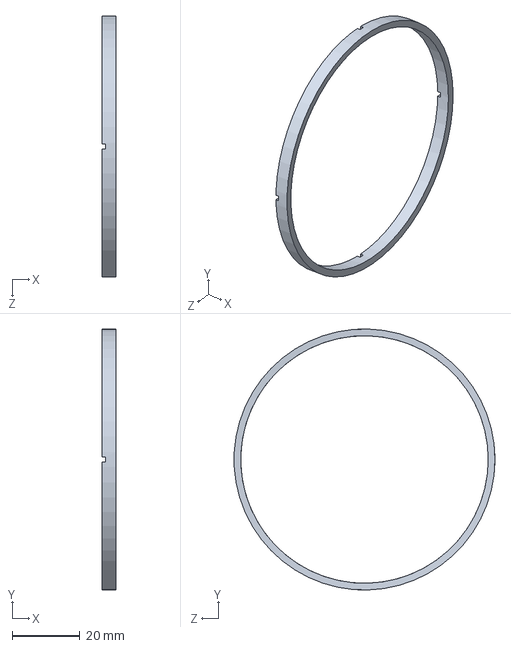
[picture p87: CAD file, 2021-04-27]
CAD/TKC_003.SLDPRT
4.00 x 77.0 x 77.0 mm
