Kubiczek36/TKC/CAD/step_30836.step

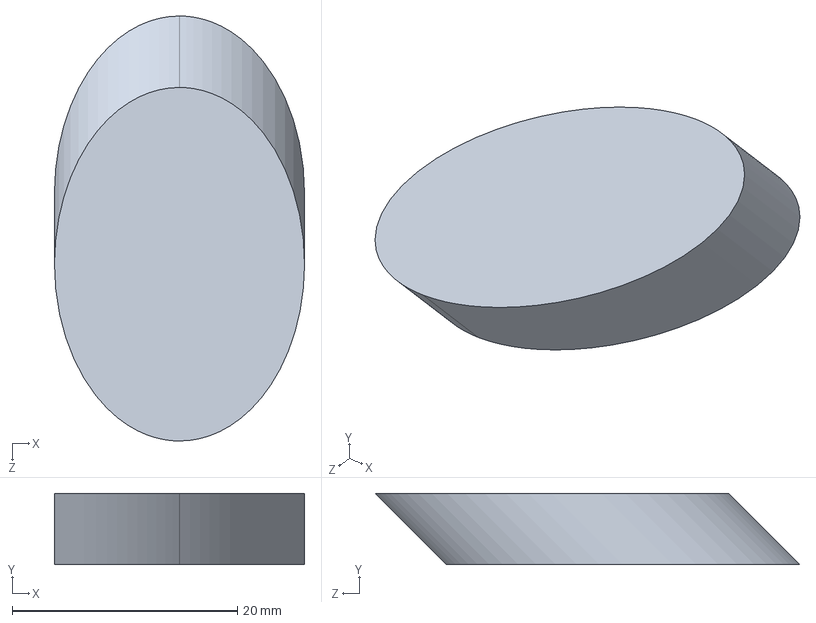
[picture p88: CAD file, 2021-04-02]
CAD/step_30836.step
22.2 x 6.35 x 37.8 mm
