Kubiczek36/TKC/CAD/drawings/TKC_000_prez.PDF

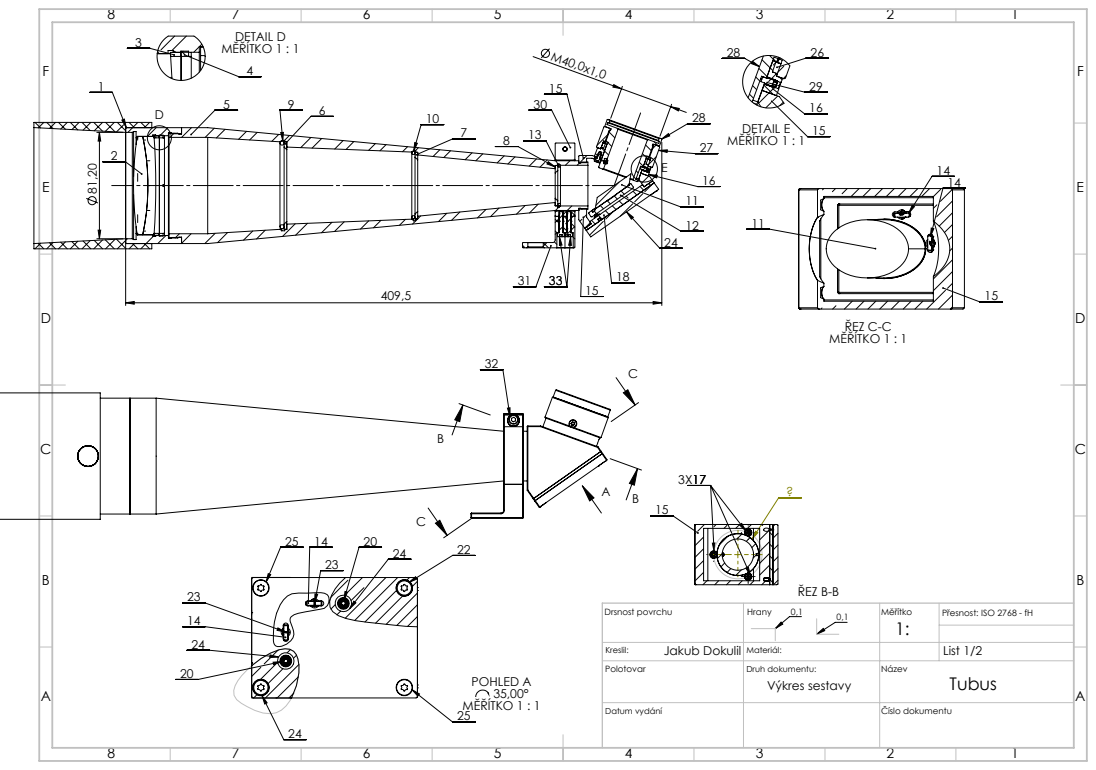
[picture p92: page 1]
POHLED A 35,00° MĚŘÍTKO 1 : 1; ŘEZ B-B; DETAIL D MĚŘÍTKO 1 : 1 3; DETAIL E MĚŘÍTKO 1 : 1; ŘEZ C-C MĚŘÍTKO 1 : 1

Drsnost povrchu | Hrany 0,1 | Měřítko 1: | Přesnost: ISO 2768 - fH 0,1

Kreslil: Jakub Dokulil | Materiál: | | List 1/2
Polotovar | Druh dokumentu: Výkres sestavy | Název Tubus

Datum vydání | | Číslo dokumentu

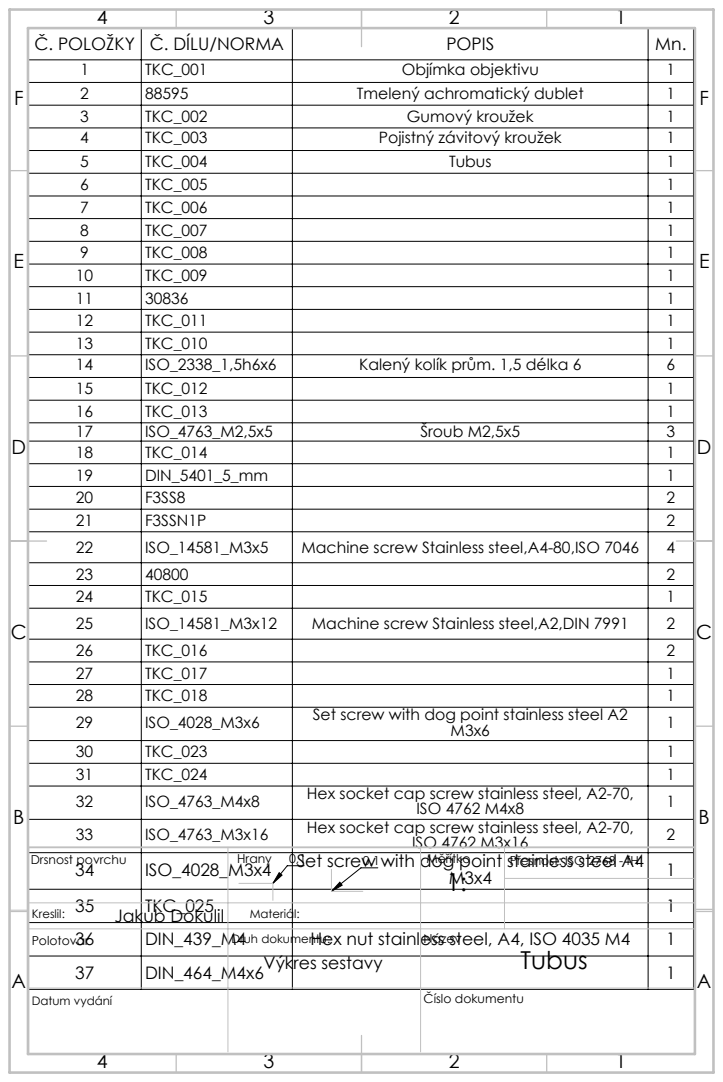
[picture p93: page 2]
Č. POLOŽKY Č. DÍLU/NORMA; POPIS; TKC_001; Objímka objektivu; Tmelený achromatický dublet; TKC_002; Gumový kroužek; TKC_003; Pojistný závitový kroužek; ISO_2338_1,5h6x6; Kalený kolík prům. 1,5 délka 6; ISO_4763_M2,5x5; Šroub M2,5x5; ISO_14581_M3x5; Machine screw Stainless steel,A4-80,ISO 7046; ISO_14581_M3x12; Machine screw Stainless steel,A2,DIN 7991; ISO_4028_M3x6; Set screw with dog point stainless steel A2; ISO_4763_M4x8; Hex socket cap screw stainless steel, A2-70,; ISO 4762 M4x8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

Jakub Dokulil Kreslil: | Materiál:
36 DIN_439_M4 Polotovar 37 DIN_464_M4x6 | Hex nut stainless steel, A4, ISO 4035 M4 Druh dokumentu: | 1 Název Tubus 1 Výkres sestavy

Datum vydání | | Číslo dokumentu

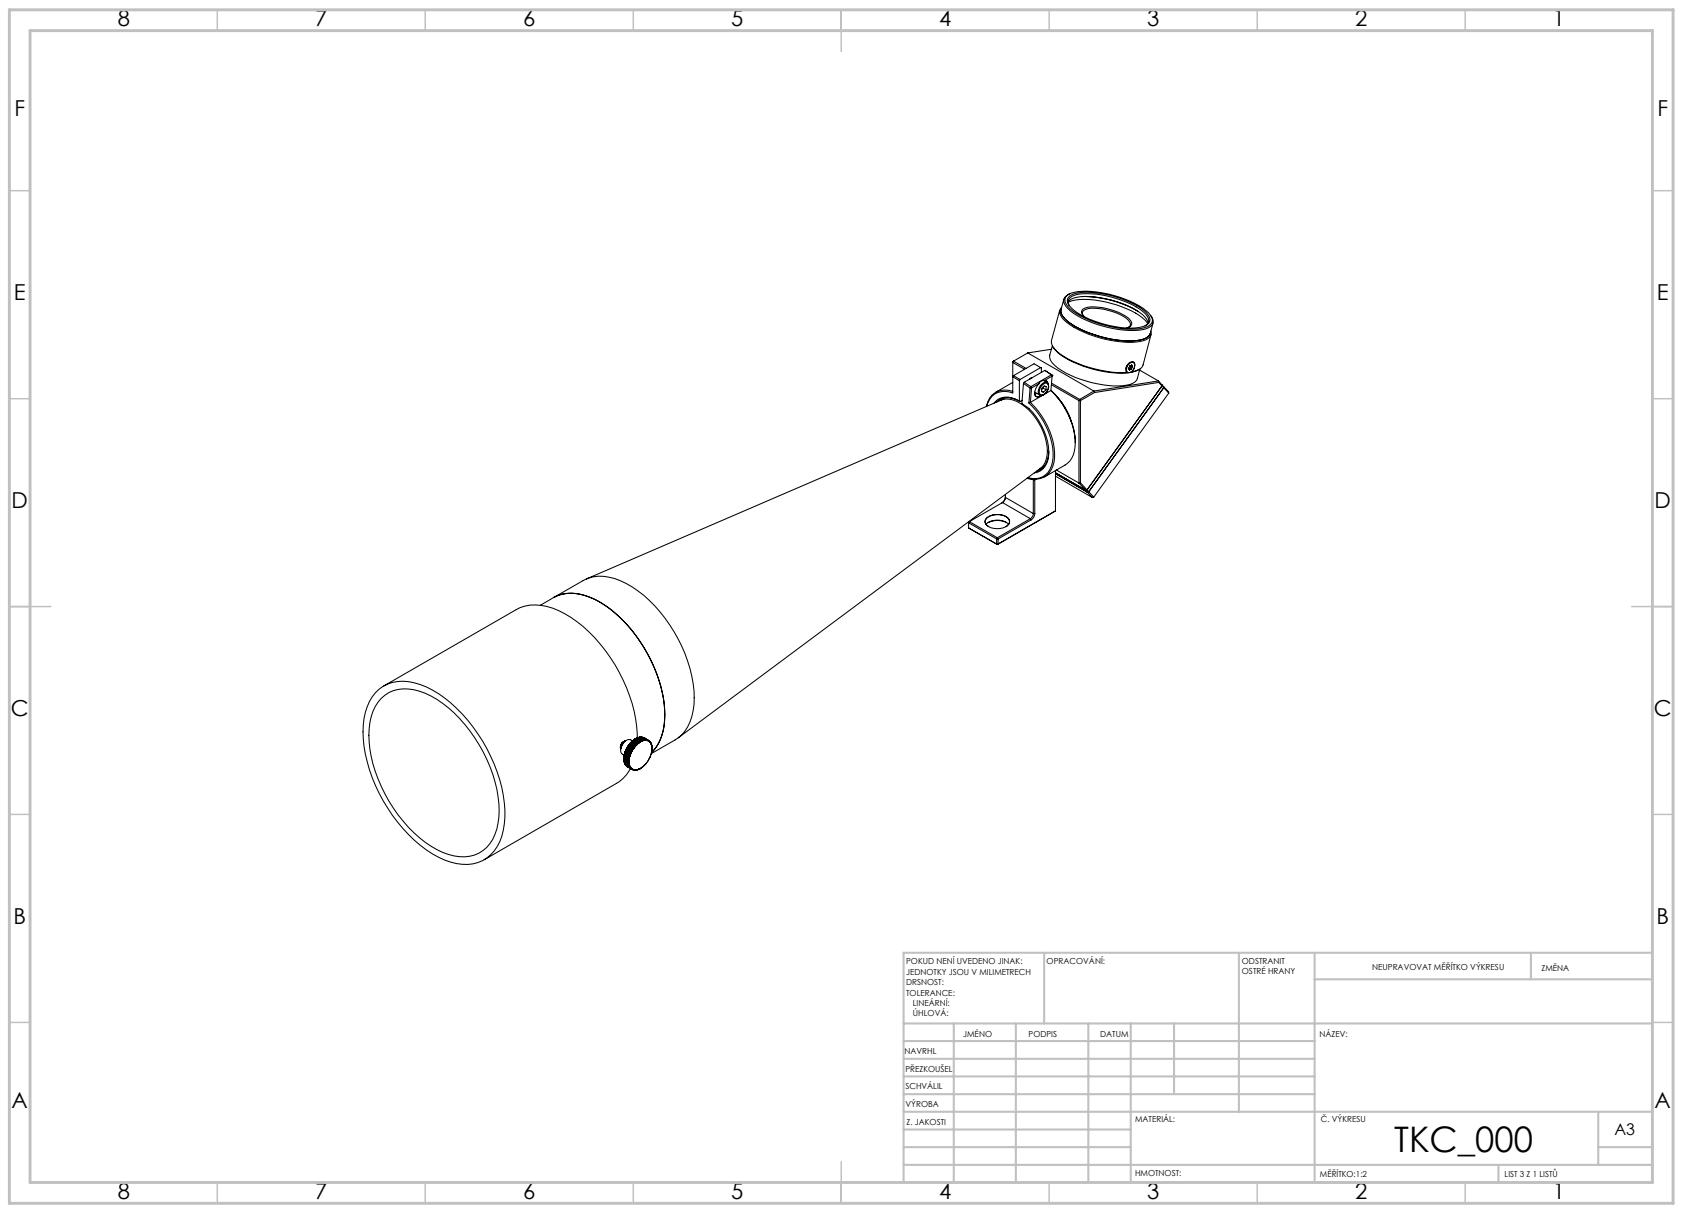
[picture p94: page 3]
MĚŘÍTKO:1:2; LIST 3 Z 1 LISTŮ; NEUPRAVOVAT MĚŘÍTKO VÝKRESU; ZMĚNA; OSTRÉ HRANY; POKUD NENÍ UVEDENO JINAK:; OPRACOVÁNÍ:; JEDNOTKY JSOU V MILIMETRECH

JMÉNO | PODPIS | DATUM | | | | NÁZEV:

NAVRHL
PŘEZKOUŠEL
SCHVÁLIL
VÝROBA
Z. JAKOSTI | | | | MATERIÁL: | Č. VÝKRESU TKC_000 HMOTNOST: | A3

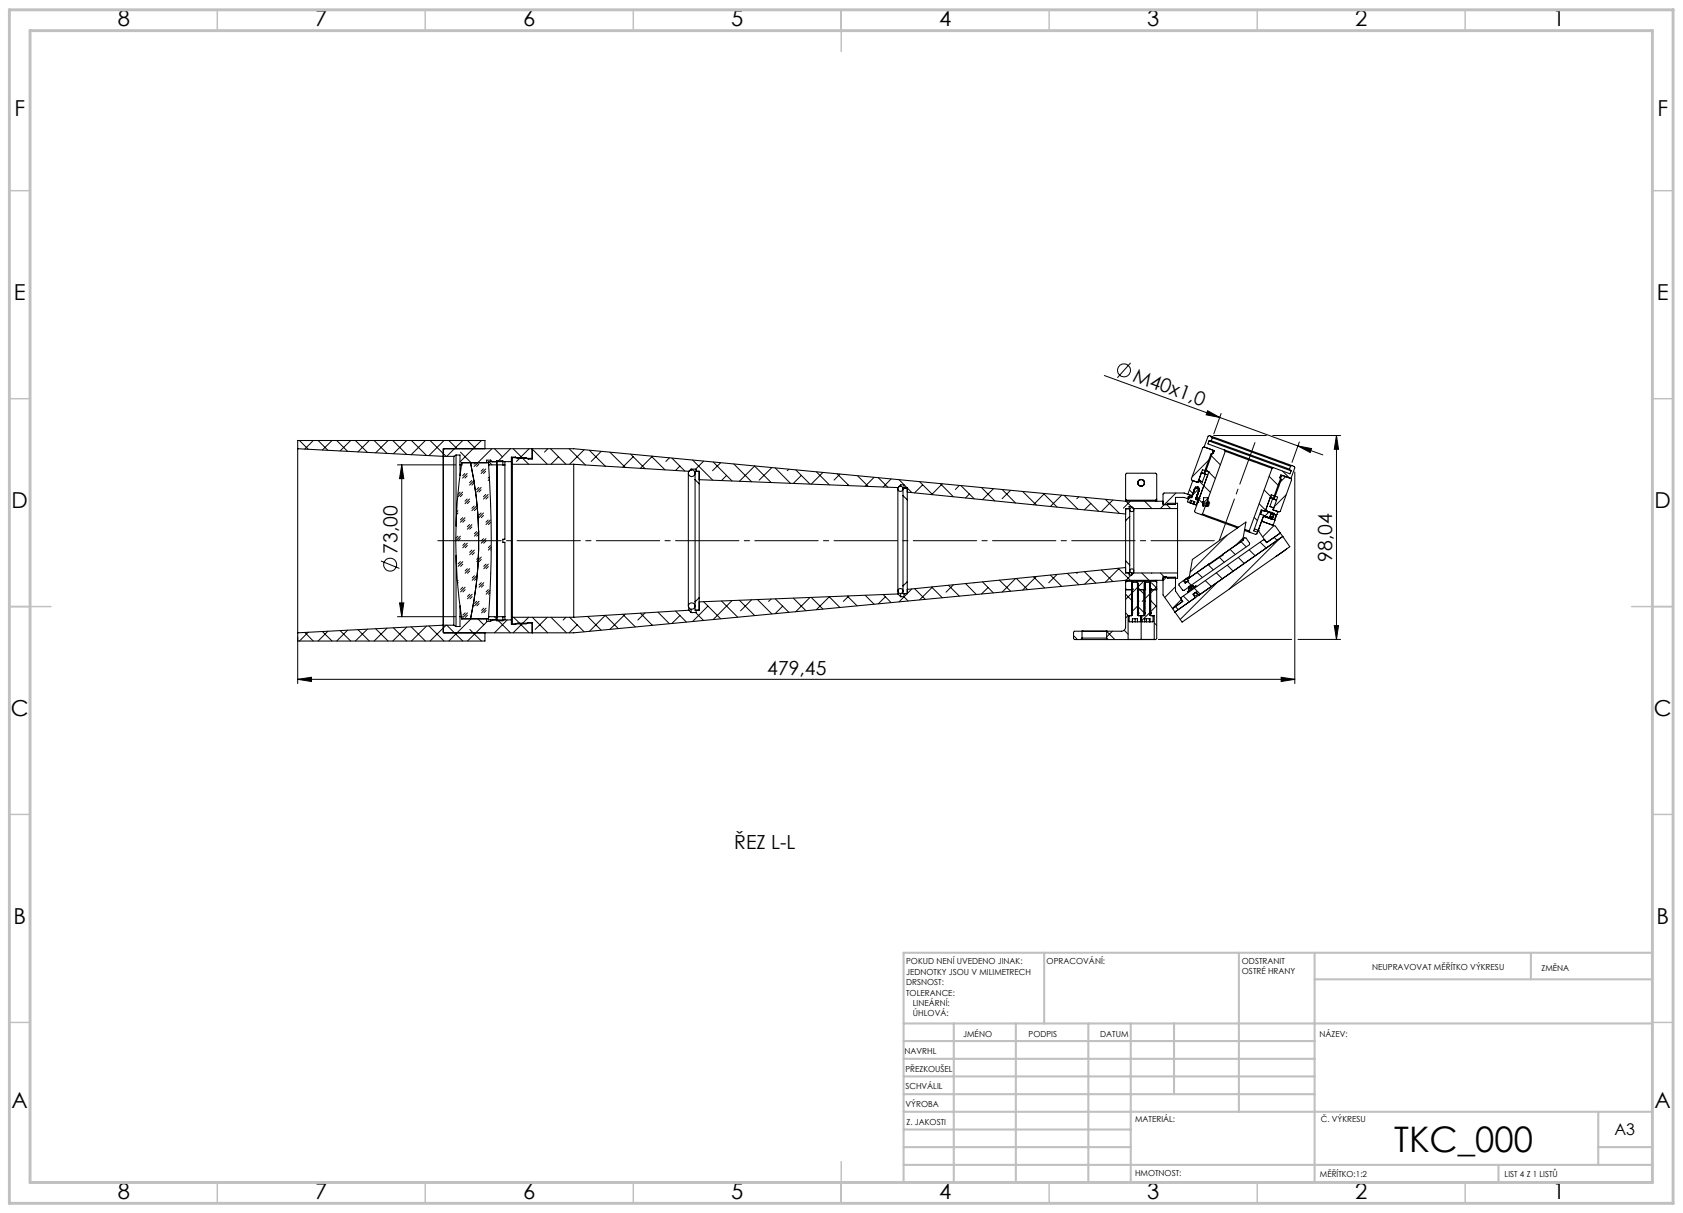
[picture p95: page 4]
ŘEZ L-L; MĚŘÍTKO:1:2; LIST 4 Z 1 LISTŮ; NEUPRAVOVAT MĚŘÍTKO VÝKRESU; ZMĚNA; OSTRÉ HRANY; POKUD NENÍ UVEDENO JINAK:; OPRACOVÁNÍ:; JEDNOTKY JSOU V MILIMETRECH

JMÉNO | PODPIS | DATUM | NÁZEV:

NAVRHL
PŘEZKOUŠEL
SCHVÁLIL
VÝROBA

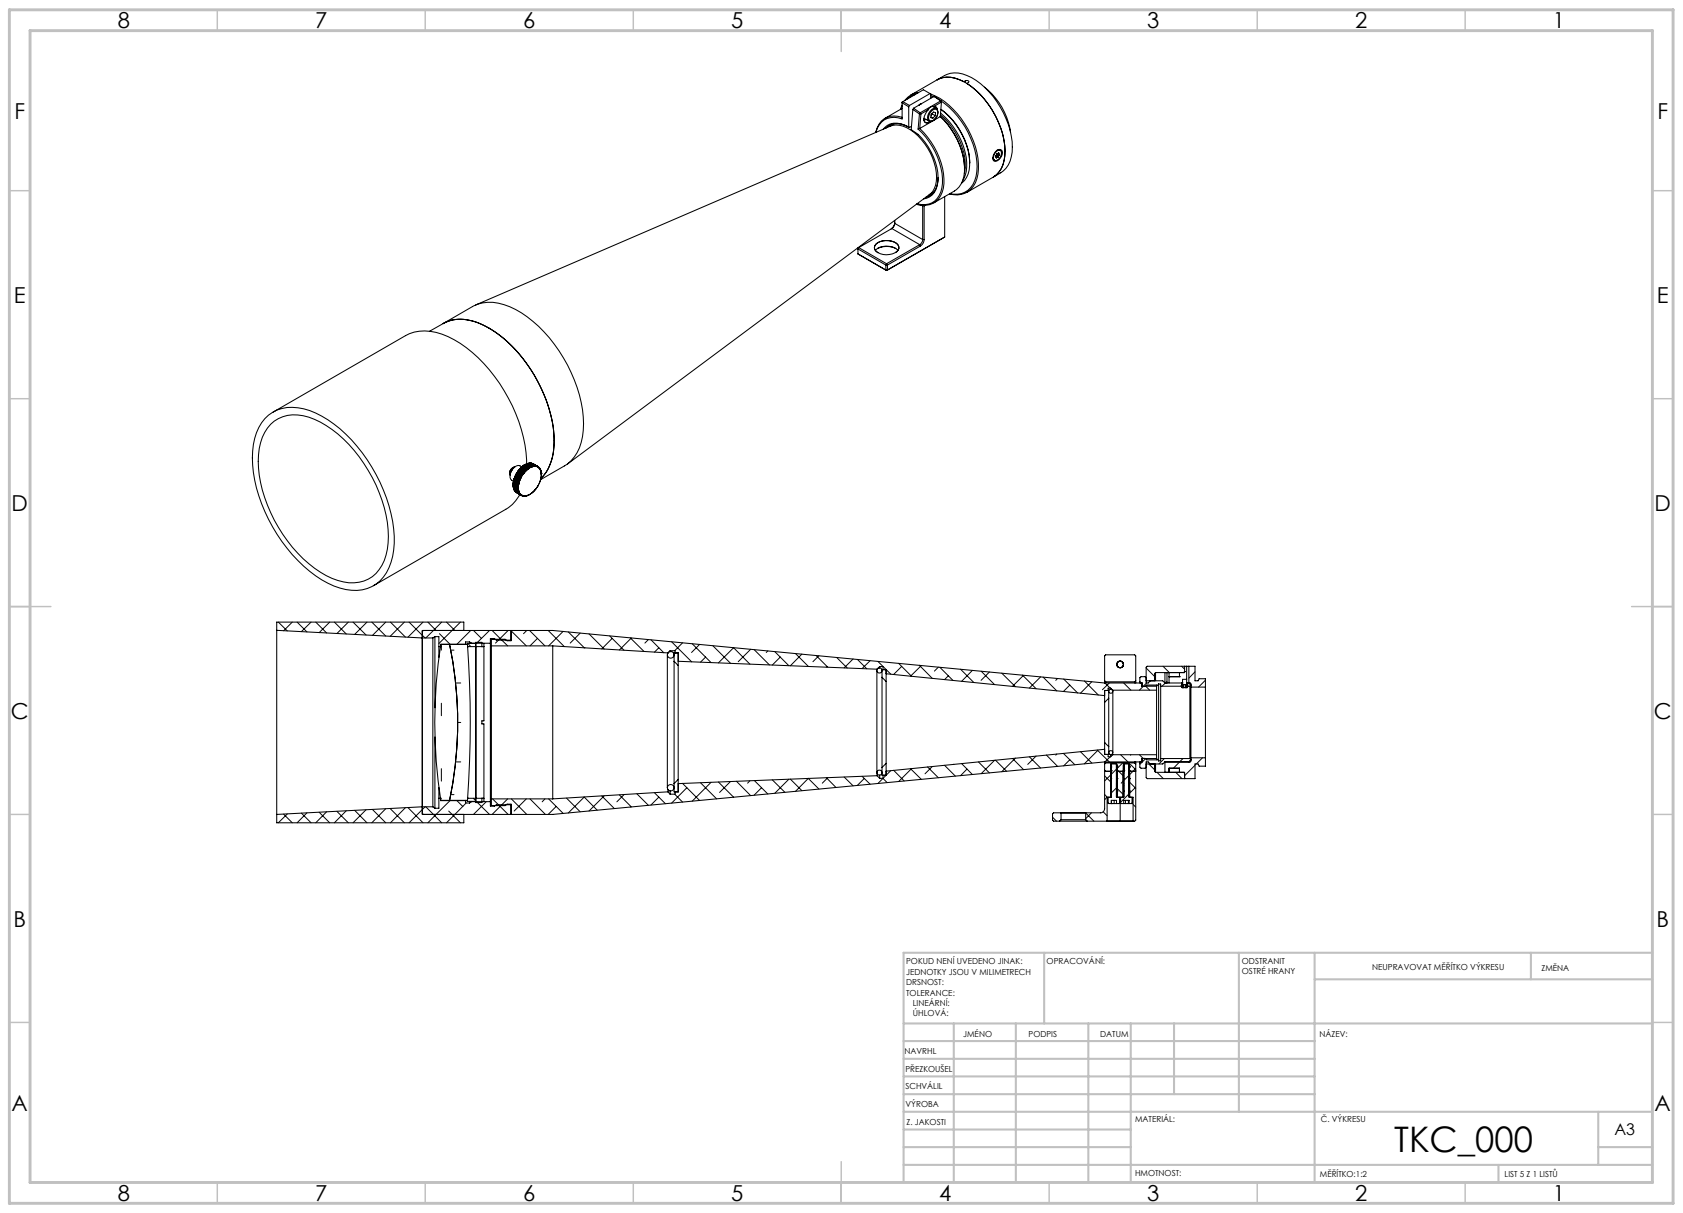
[picture p96: page 5]
MĚŘÍTKO:1:2; LIST 5 Z 1 LISTŮ; NEUPRAVOVAT MĚŘÍTKO VÝKRESU; ZMĚNA; OSTRÉ HRANY; POKUD NENÍ UVEDENO JINAK:; OPRACOVÁNÍ:; JEDNOTKY JSOU V MILIMETRECH

JMÉNO | PODPIS | DATUM | NÁZEV:

NAVRHL
PŘEZKOUŠEL
SCHVÁLIL
VÝROBA
