Kubiczek36/TKC/CAD/drawings/TKC_012.PDF

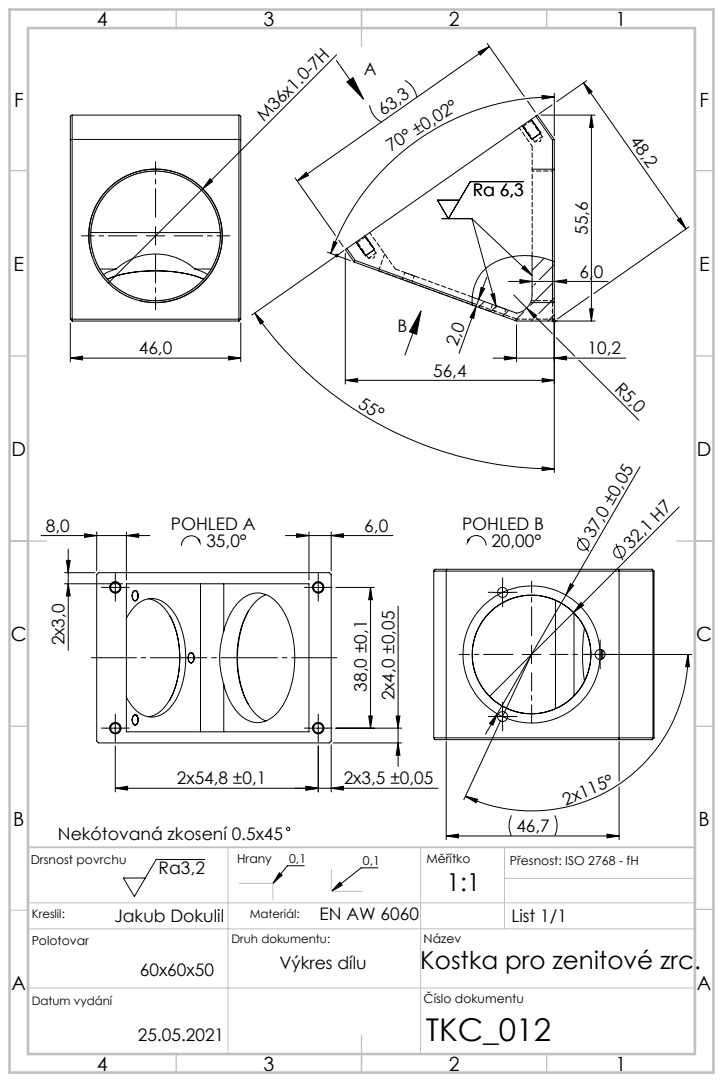
[picture p101: page 1]
POHLED A; POHLED B; Nekótovaná zkosení 0.5x45; Drsnost povrchu; Hrany 0,1; Měřítko; Přesnost: ISO 2768 - fH

Jakub Dokulil Kreslil: | EN AW 6060 Materiál: | | List 1/1
Polotovar 60x60x50 | Druh dokumentu: Výkres dílu | Název Kostka pro zenitové zrc.

Datum vydání 25.05.2021 | | Číslo dokumentu TKC_012
