Kubiczek36/TKC/CAD/drawings/TKC_013.PDF

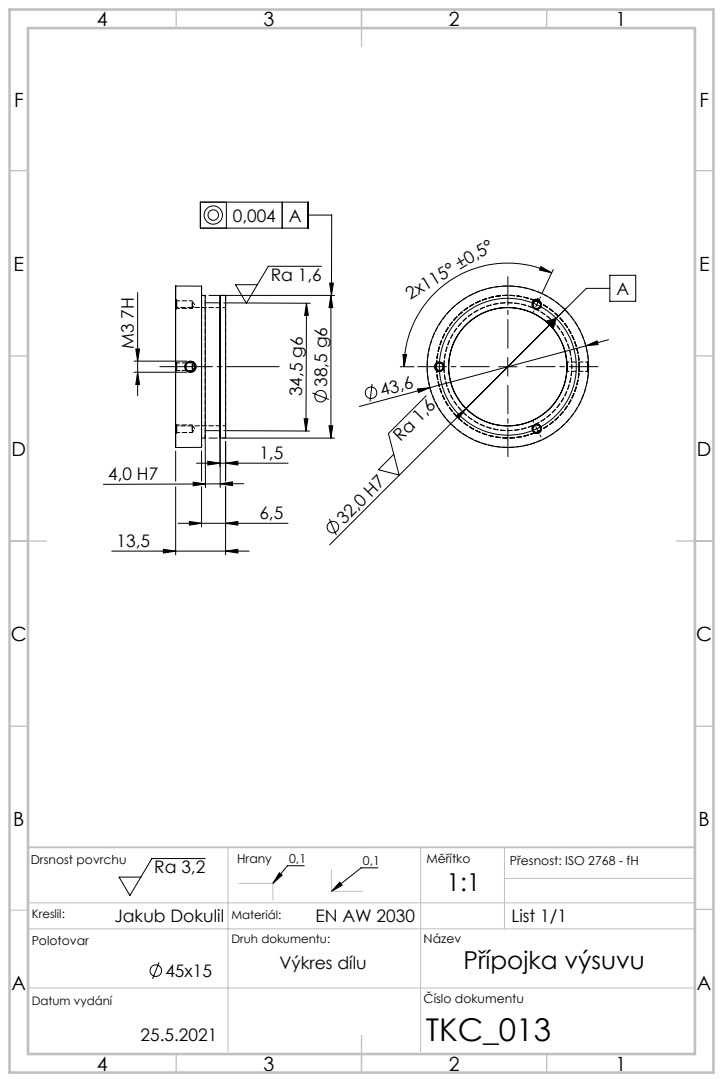
[picture p102: page 1]
Drsnost povrchu; Hrany 0,1; Měřítko; Přesnost: ISO 2768 - fH

Jakub Dokulil Kreslil: | EN AW 2030 Materiál: | | List 1/1
Polotovar 45x15 | Druh dokumentu: Výkres dílu | Název Přípojka výsuvu

Datum vydání 25.5.2021 | | Číslo dokumentu TKC_013
