Kubiczek36/TKC/CAD/drawings/TKC_014.PDF

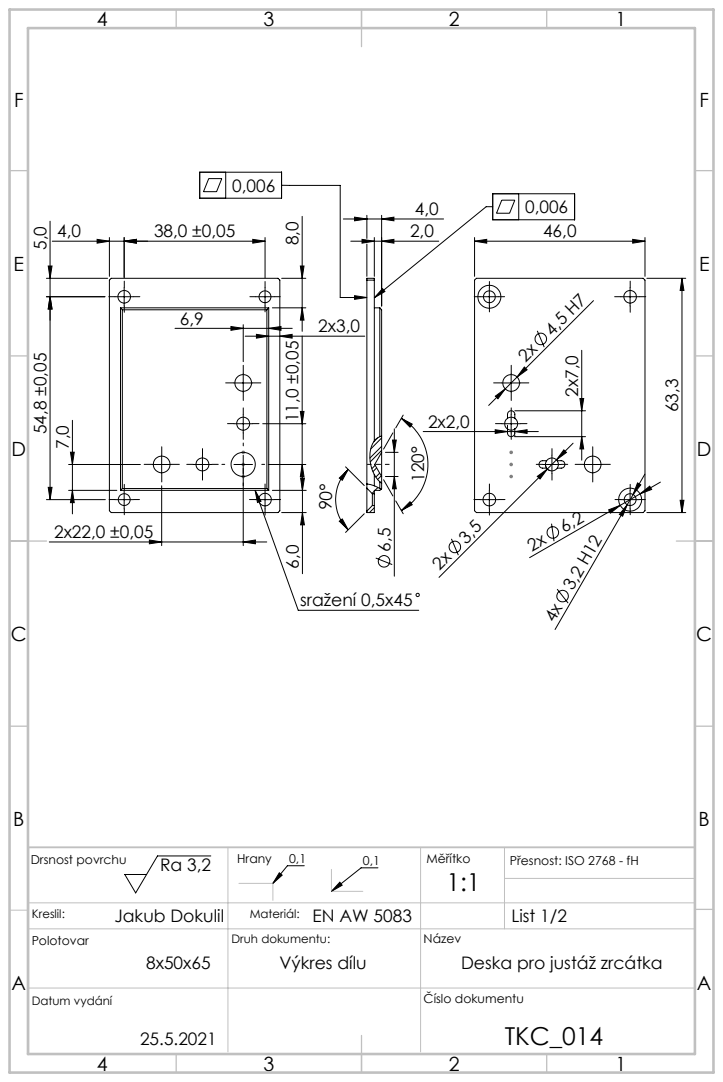
[picture p103: page 1]
sražení 0,5x45; Drsnost povrchu; Hrany 0,1; Měřítko; Přesnost: ISO 2768 - fH

Jakub Dokulil Kreslil: | Materiál: EN AW 5083 | | List 1/2
Polotovar 8x50x65 | Druh dokumentu: Výkres dílu | Název Deska pro justáž zrcátka

Datum vydání 25.5.2021 | | Číslo dokumentu TKC_014
