Kubiczek36/TKC/CAD/drawings/TKC_015.PDF

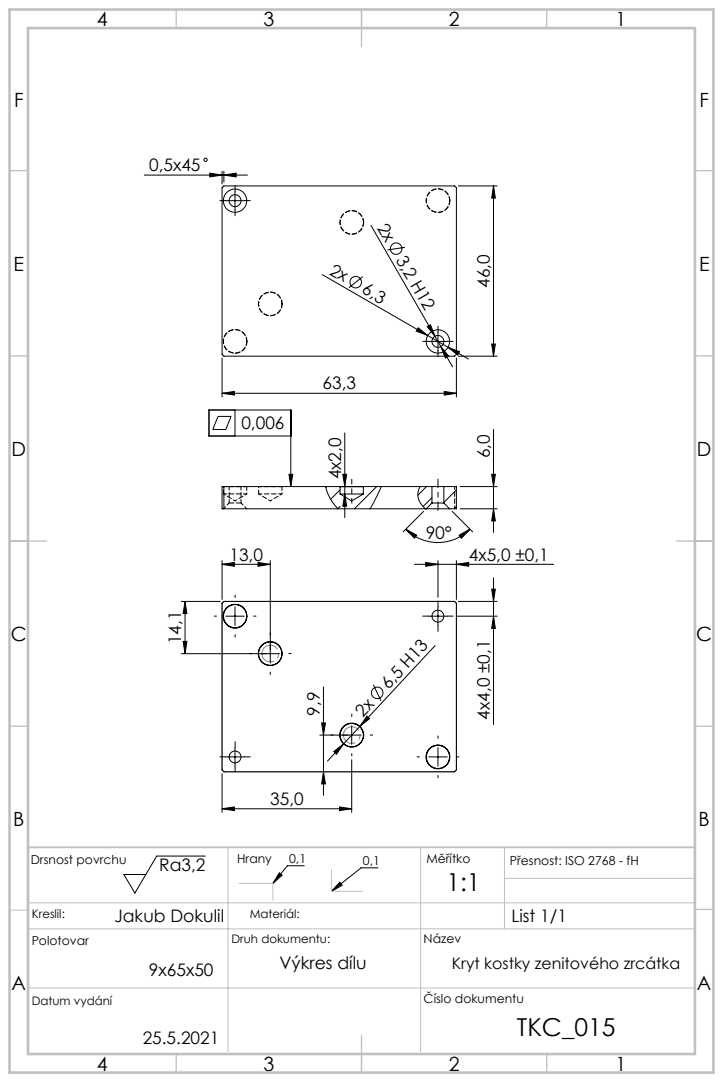
[picture p104: page 1]
Drsnost povrchu; Hrany 0,1; Měřítko; Přesnost: ISO 2768 - fH

Jakub Dokulil Kreslil: | Materiál: | | List 1/1
Polotovar 9x65x50 | Druh dokumentu: Výkres dílu | Název Kryt kostky zenitového zrcátka

Datum vydání 25.5.2021 | | Číslo dokumentu TKC_015
